akashlevy/NEM-Relay-CAD/figures/3d-cgra.pdf

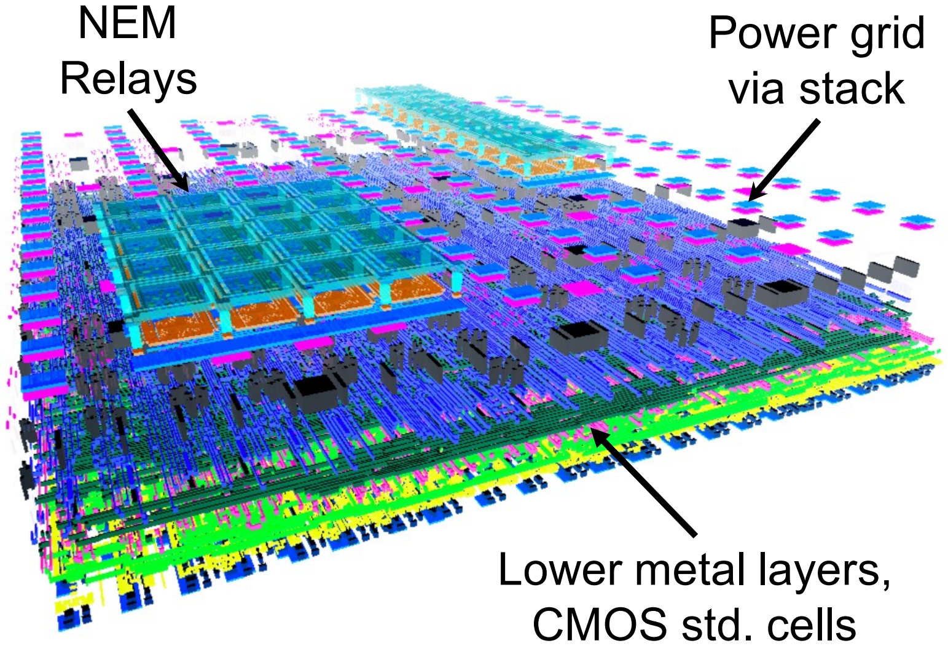
[picture p6: page 1]

NEM
Relays

Lower metal layers,
CMOS std. cells

Power grid
via stack
