akashlevy/NEM-Relay-CAD/figures/area-utilization.pdf

[7] This
work

Plate
Area
Total
Area

+40%
area util.

Area utilization: 0.33 Area utilization: 0.54
