akashlevy/NEM-Relay-CAD/figures/nem-mux-1.pdf

## Input Bits

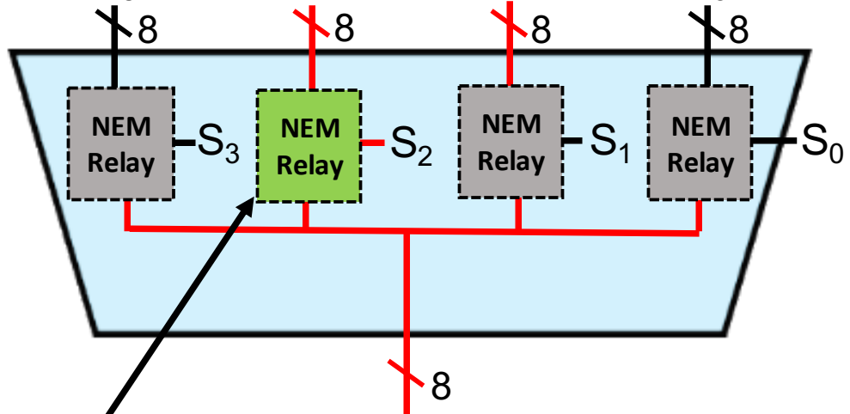
[picture p7: figure]
NEM Relay

## NEM Relay One-Hot

Output Bits | Mux (8-bit)

Example Signals:
Red=Hi, Black=Lo

Relays:
Green=ON state
Gray=OFF state

## I0 I1 I2 I3

Z

### Relay passes signal I2 through to Z pin
