akashlevy/NEM-Relay-CAD/figures/ppa-benefits.pdf

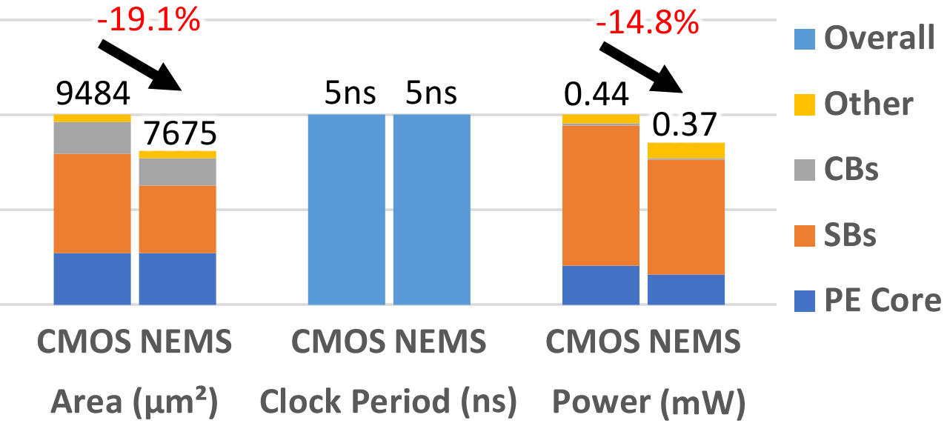
[picture p8: figure]
CMOS NEMS; Area (µm²) Clock Period; Power; Overall Other CBs SBs PE Core
