akashlevy/NEM-Relay-CAD/figures/nem-mux-2.pdf

## NEM Relay Implementation

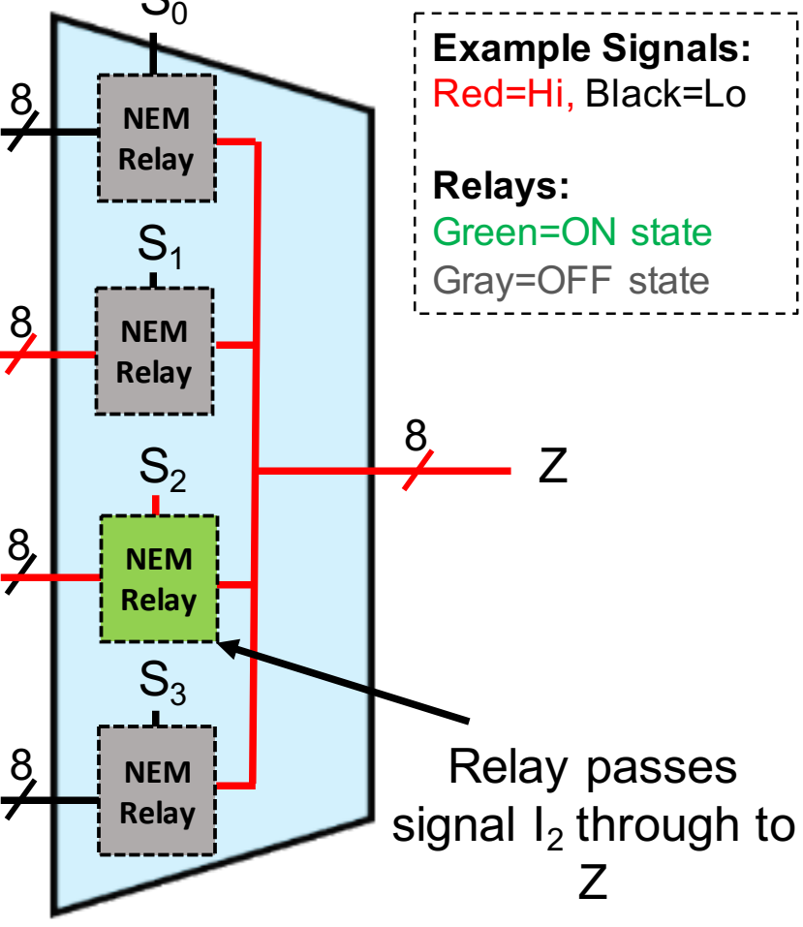
[picture p9: figure]
Example Signals: Red=Hi, Black=Lo; Relays: Green=ON state Gray=OFF state; NEM Relay; Relay passes signal I2 through to Z

I0

I1

I2

I3

S0
