akashlevy/NEM-Relay-CAD/figures/nem-mux-3.pdf

## NEM Relay Implementation

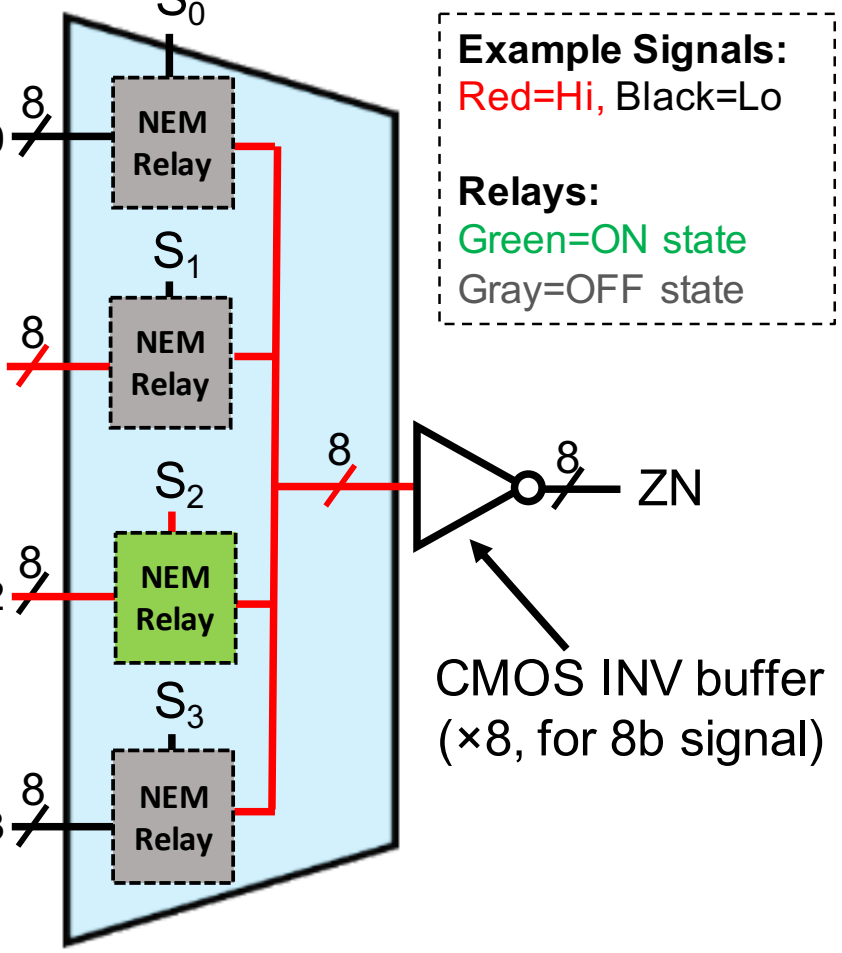
[picture p10: figure]
Example Signals: Red=Hi, Black=Lo; Relays: Green=ON state Gray=OFF state; NEM Relay; CMOS INV buffer (×8, for 8b signal)

I0

I1

I2

I3

S0
