akashlevy/NEM-Relay-CAD/figures/nem-mux-internals.pdf

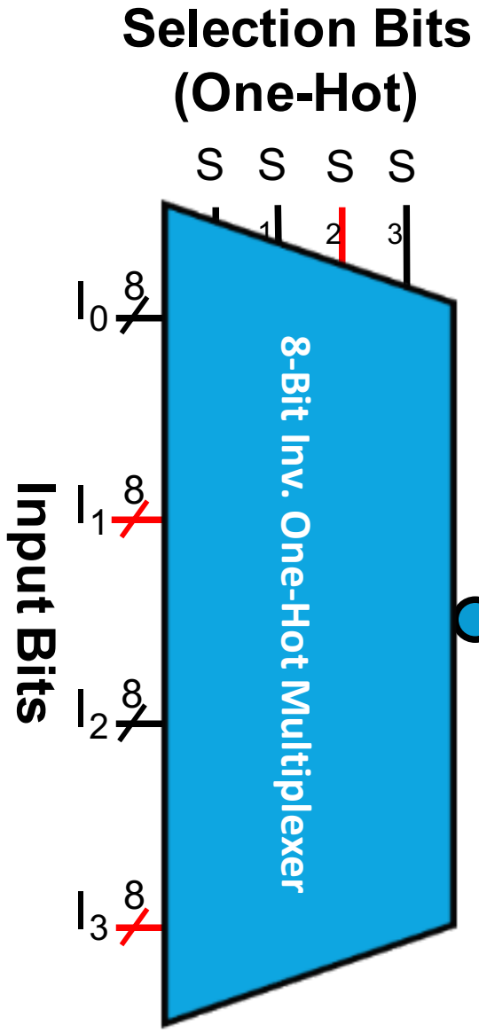
[picture p11: figure]
Selection Bits (One-Hot); Input Bits; 8 -Bit Inv. One; -Hot Multiplexer
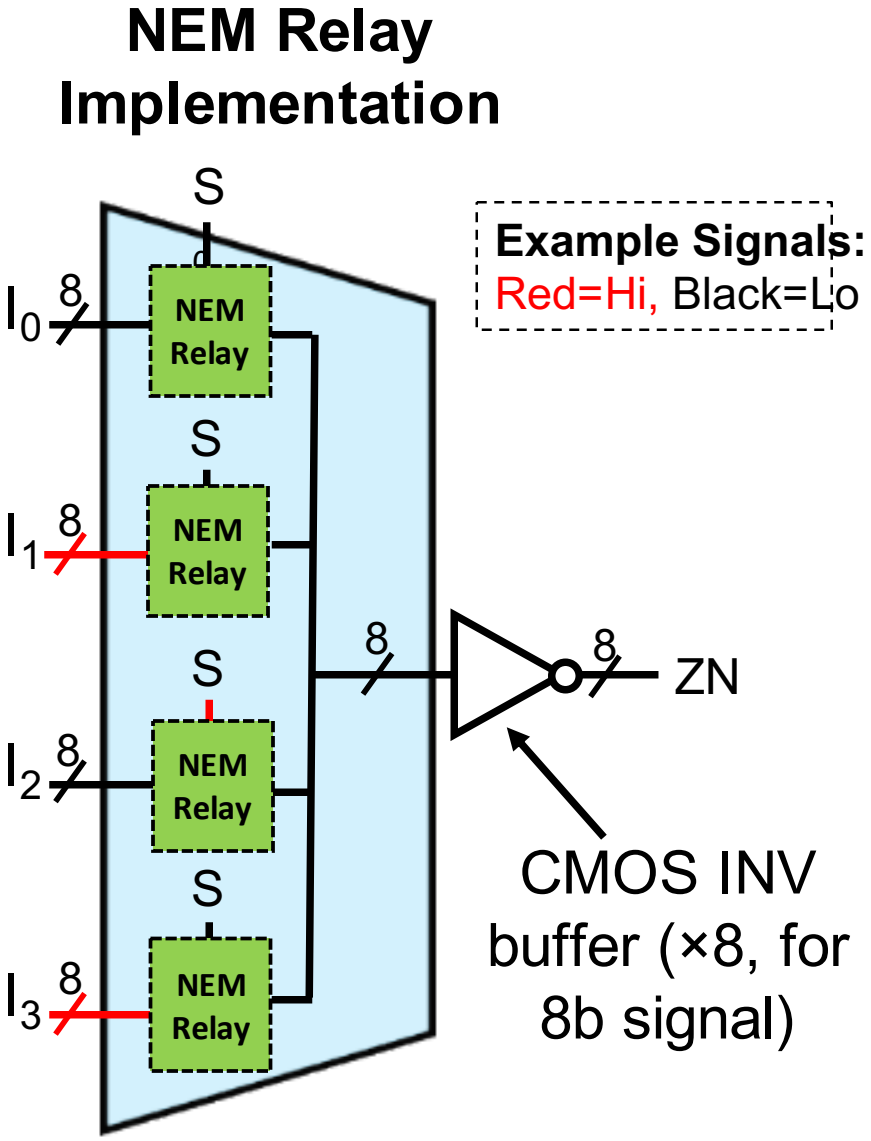
[picture p12: figure]
NEM Relay Implementation; Example Signals: Red=Hi, Black=Lo I0; NEM Relay; CMOS INV buffer (×8, for 8b signal)

8
ZN

Output Bits
