akashlevy/NEM-Relay-CAD/figures/nems-mux-3.pdf

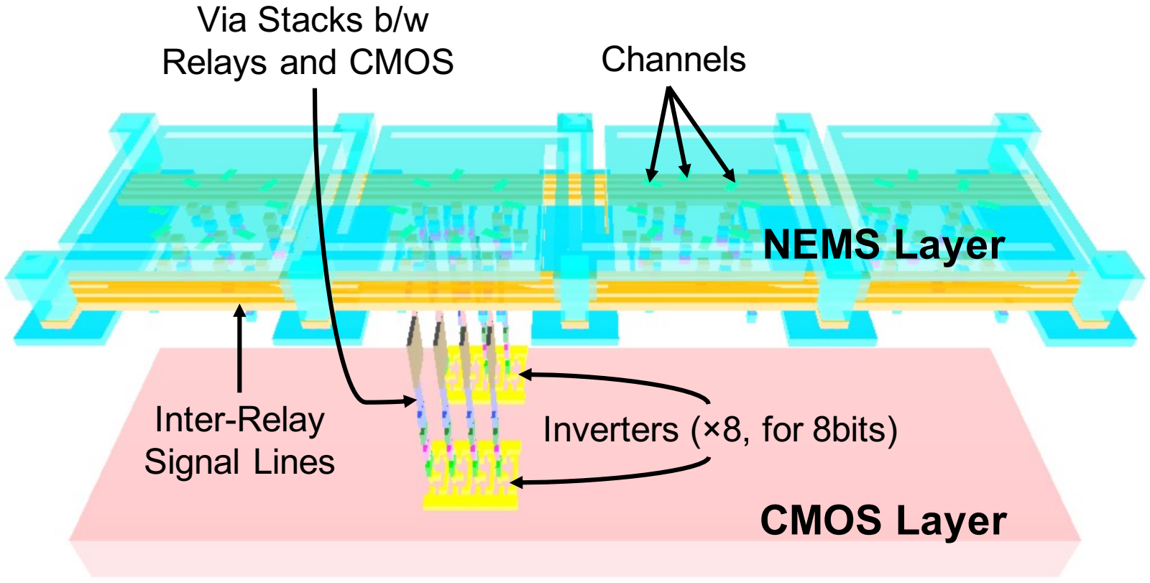
[picture p13: page 1]

CMOS Layer

NEMS Layer

Inter-Relay
Signal Lines

Via Stacks b/w
Relays and CMOS | Channels

Inverters (×8, for 8bits)
