akashlevy/NEM-Relay-CAD/figures/power-plot.pdf

0

20

40

60

80

Total Power (mW)

Cascade Conv 3×3 | Harris CMOS NEMS | CMOS NEMS | CMOS NEMS

CBs
Other
PE Core
SB

Module
