akashlevy/NEM-Relay-CAD/figures/power.pdf

0

20

40

60

80

Total Power (mW)

CMOS

NEMS

Conv 3×3

CMOS

NEMS

Cascade

CMOS

NEMS

Harris

CBs
Other
PE Core
SB

Module
