akashlevy/NEM-Relay-CAD/figures/layout-1.pdf

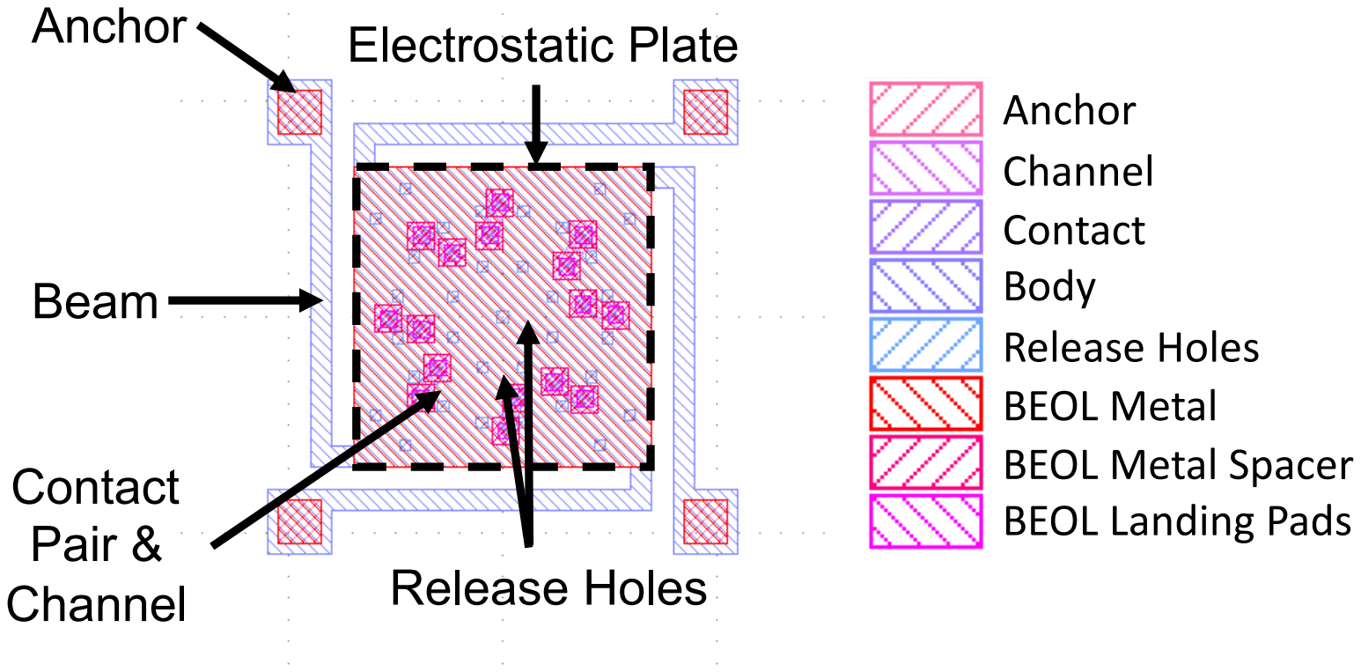
[picture p14: page 1]

Anchor
Channel
Contact
Body
Release Holes
BEOL Metal
BEOL Metal Spacer
BEOL Landing Pads

Anchor

Beam

Contact
Pair &
Channel | Release Holes

Electrostatic Plate
