akashlevy/NEM-Relay-CAD/figures/relay-layout.pdf

(a)

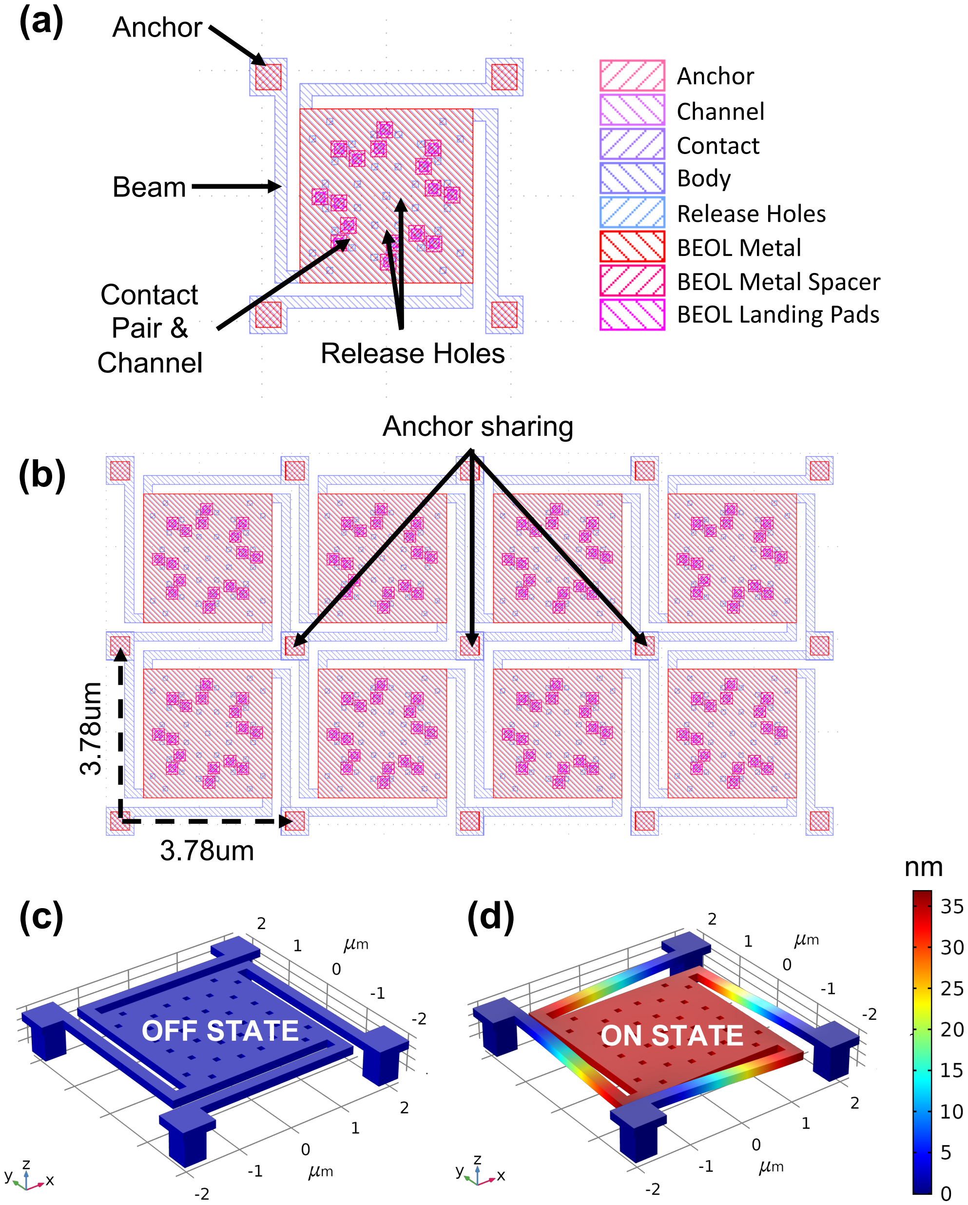
[picture p15: page 1]

Anchor
Channel
Contact
Body
Release Holes
BEOL Metal
BEOL Metal Spacer
BEOL Landing Pads

Anchor

Beam

Contact
Pair &
Channel | Release Holes

(b)

| Anchor sharing
OFF STATE | ON STATE
(c) (d)

nm

3.78u

m

3.78um
