akashlevy/NEM-Relay-CAD/figures/relay-side-view-mp-cartoon.pdf

S1 | G | D1

B

Channel

Dielectric Spacer

S2 | G | D2

Channel

G
