akashlevy/NEM-Relay-CAD/figures/transient-curve-rise.pdf

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

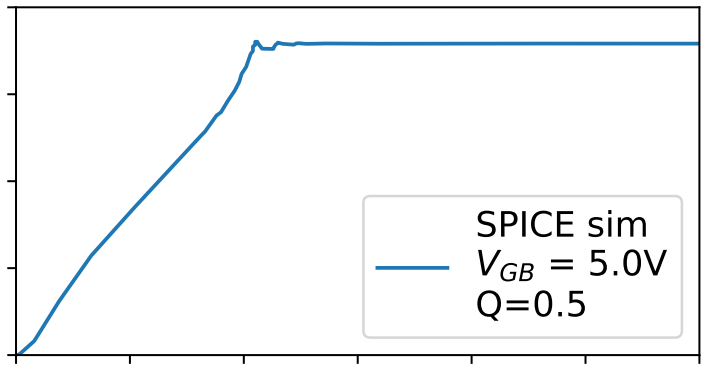
[picture p18: figure]
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
