akashlevy/NEM-Relay-CAD/figures/contact-variation.pdf

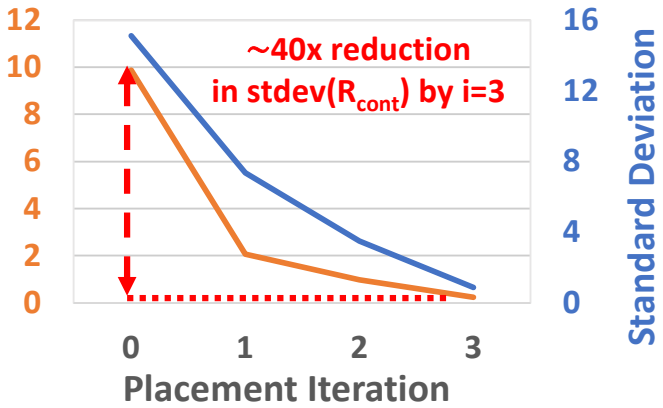
[picture p19: figure]
Standard Deviation; Placement Iteration ∼40x reduction in stdev(Rcont) by i=3

### of Fcont (nN)

Standard Deviation

### of Rcont (Ω)
