akashlevy/NEM-Relay-CAD/figures/layout-2.pdf

…

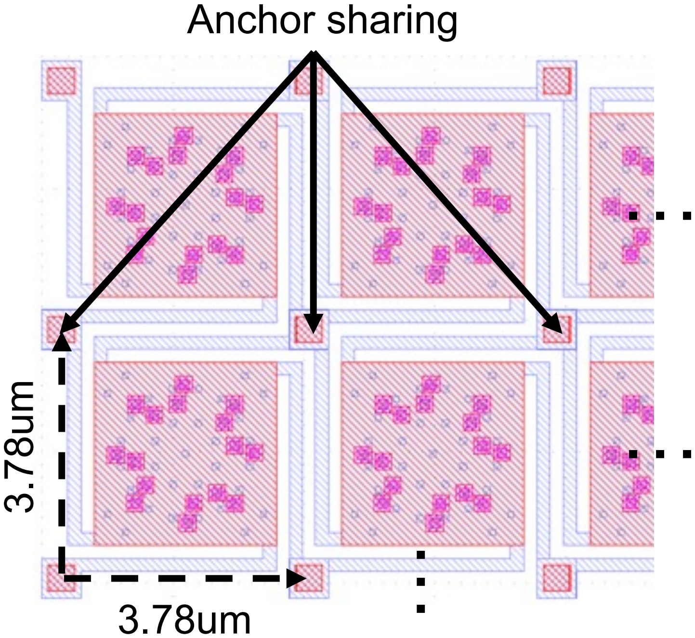
[picture p20: page 1]

Anchor sharing

3.78um

3.78um

…

…
