akashlevy/NEM-Relay-CAD/figures/area-2.pdf

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

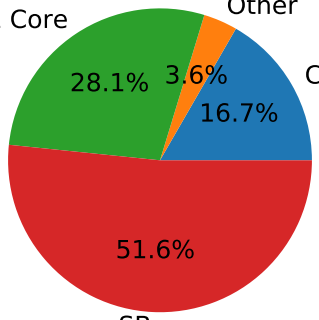
[picture p21: figure]
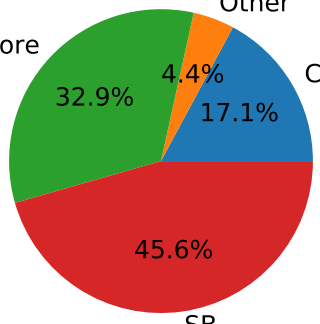
[picture p22: figure]
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
