akashlevy/NEM-Relay-CAD/figures/area-breakdown.pdf

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

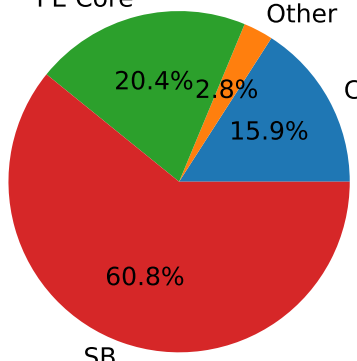
[picture p23: figure]
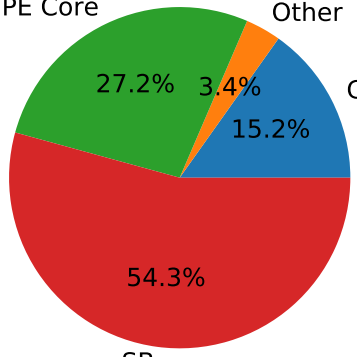
[picture p24: figure]
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
