akashlevy/NEM-Relay-CAD/figures/delay-2.pdf

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

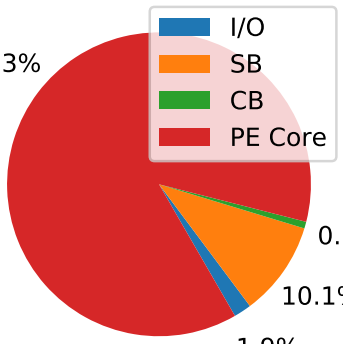
[picture p25: figure]
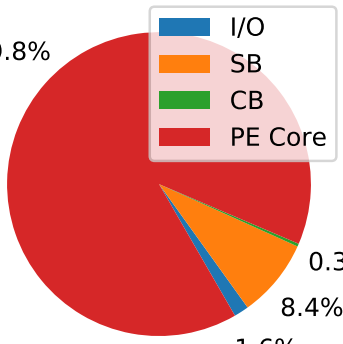
[picture p26: figure]
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
