akashlevy/NEM-Relay-CAD/figures/power-breakdown.pdf

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

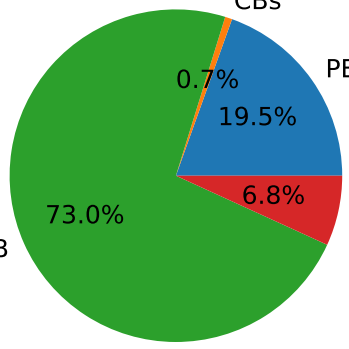
[picture p27: figure]
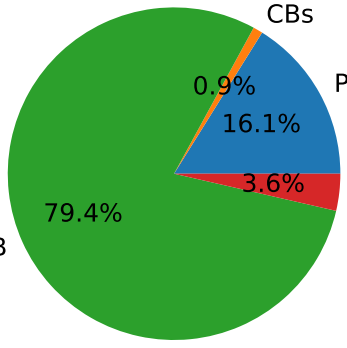
[picture p28: figure]
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
