akashlevy/NEM-Relay-CAD/figures/layout-3.pdf

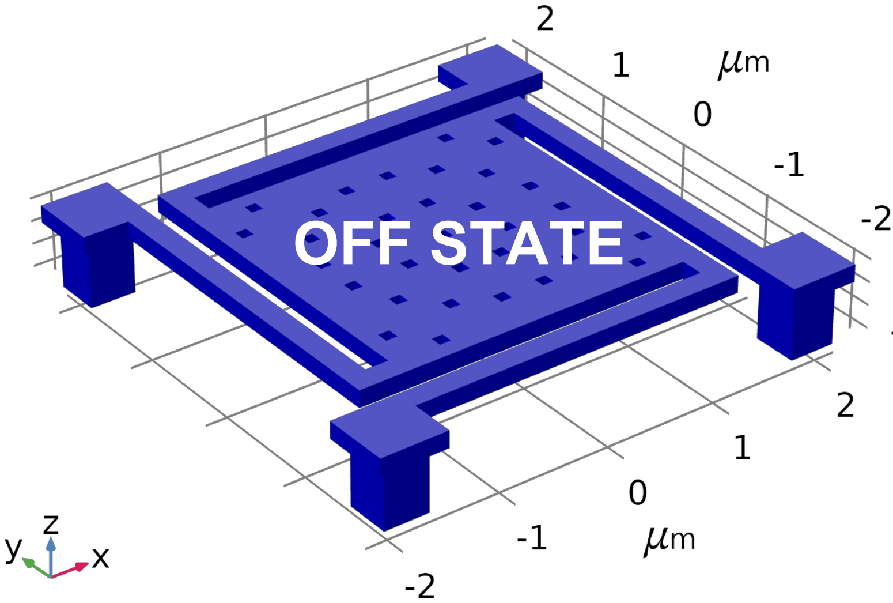
[picture p29: page 1]

OFF STATE
