akashlevy/NEM-Relay-CAD/figures/layout-4.pdf

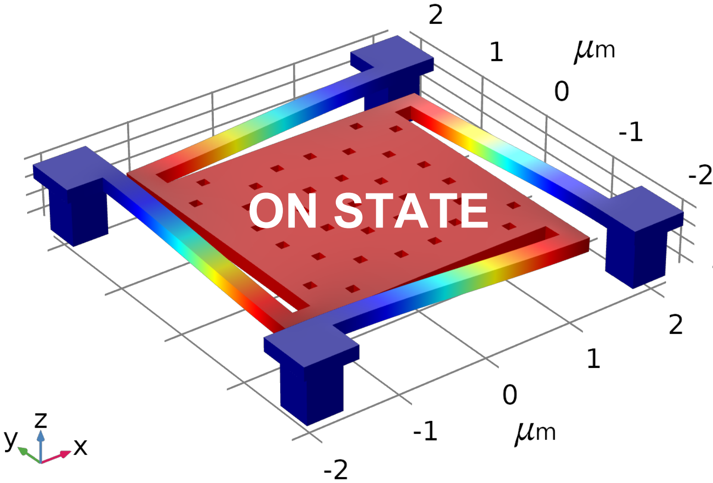
[picture p30: page 1]

ON STATE
