akashlevy/NEM-Relay-CAD/figures/layout-5.pdf

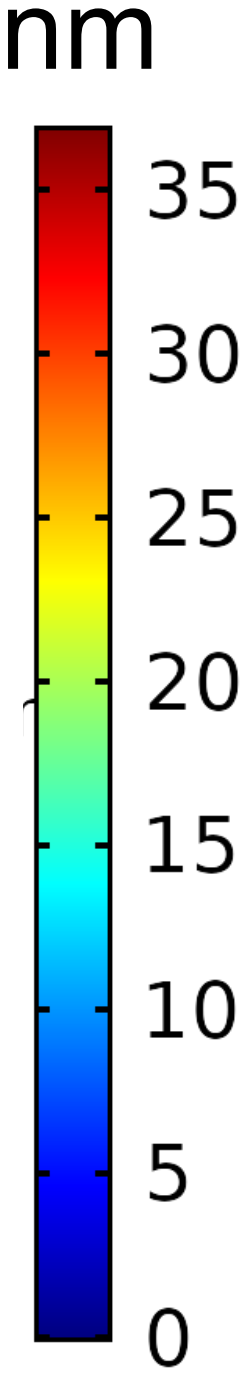
[picture p31: page 1]

nm
