akashlevy/NEM-Relay-CAD/figures/iterative-contact-placement.pdf

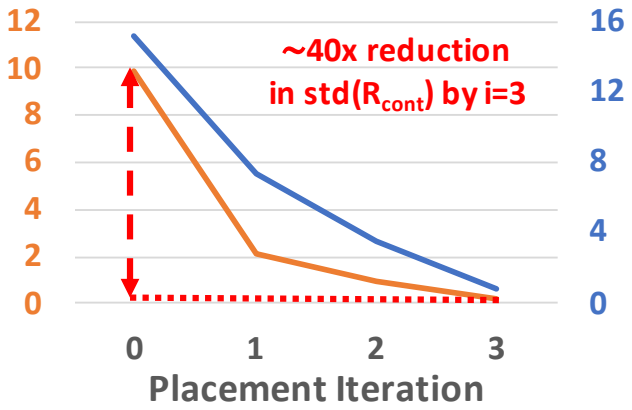
[picture p32: figure]
Placement Iteration ∼40x reduction in std(Rcont) by i=3

### Std. of Fcont (nN)

### Std. of Rcont (Ω)
