akashlevy/NEM-Relay-CAD/figures/3d-cgra.png

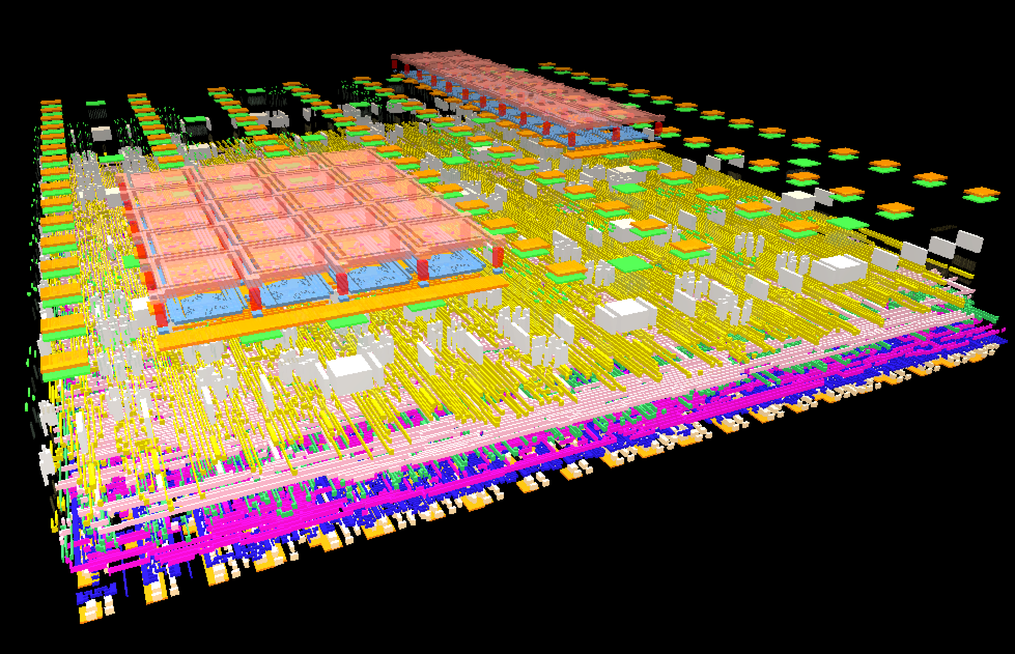
figures/3d-cgra.png
