akashlevy/NEM-Relay-CAD/figures/cccp-hor.png

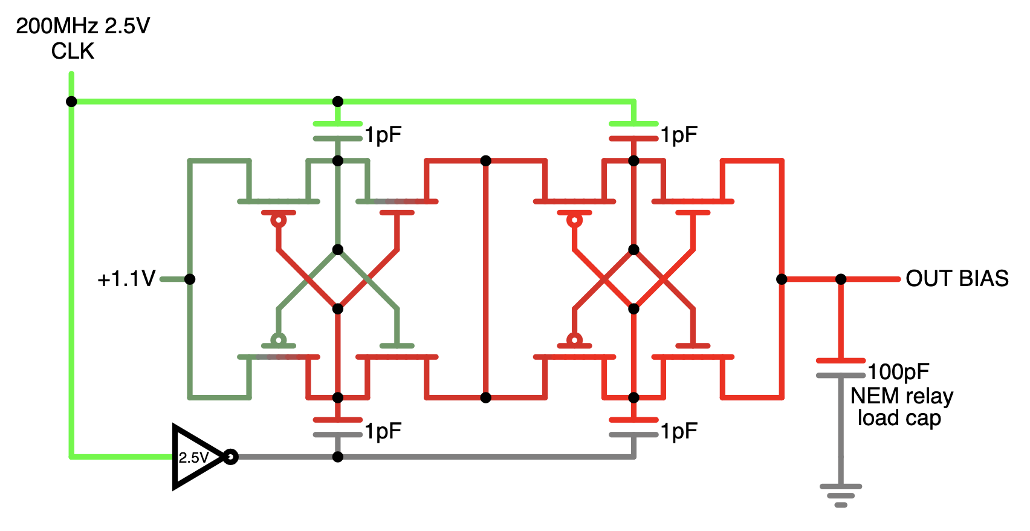
figures/cccp-hor.png
