akashlevy/NEM-Relay-CAD/figures/cccp-vert.png

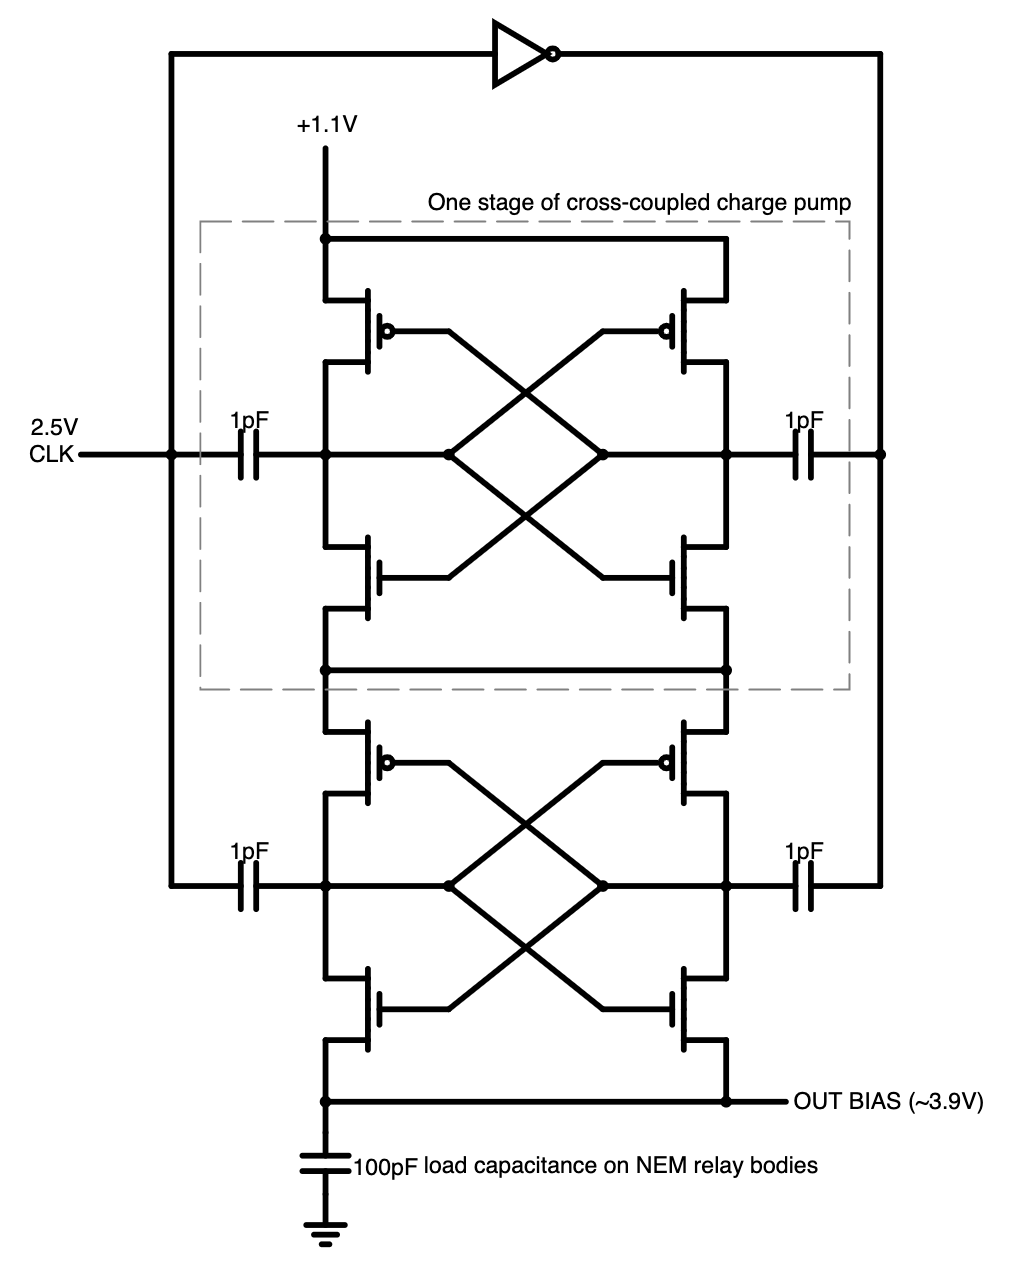
figures/cccp-vert.png
