akashlevy/NEM-Relay-CAD/figures/cpump-diode-circuit.png

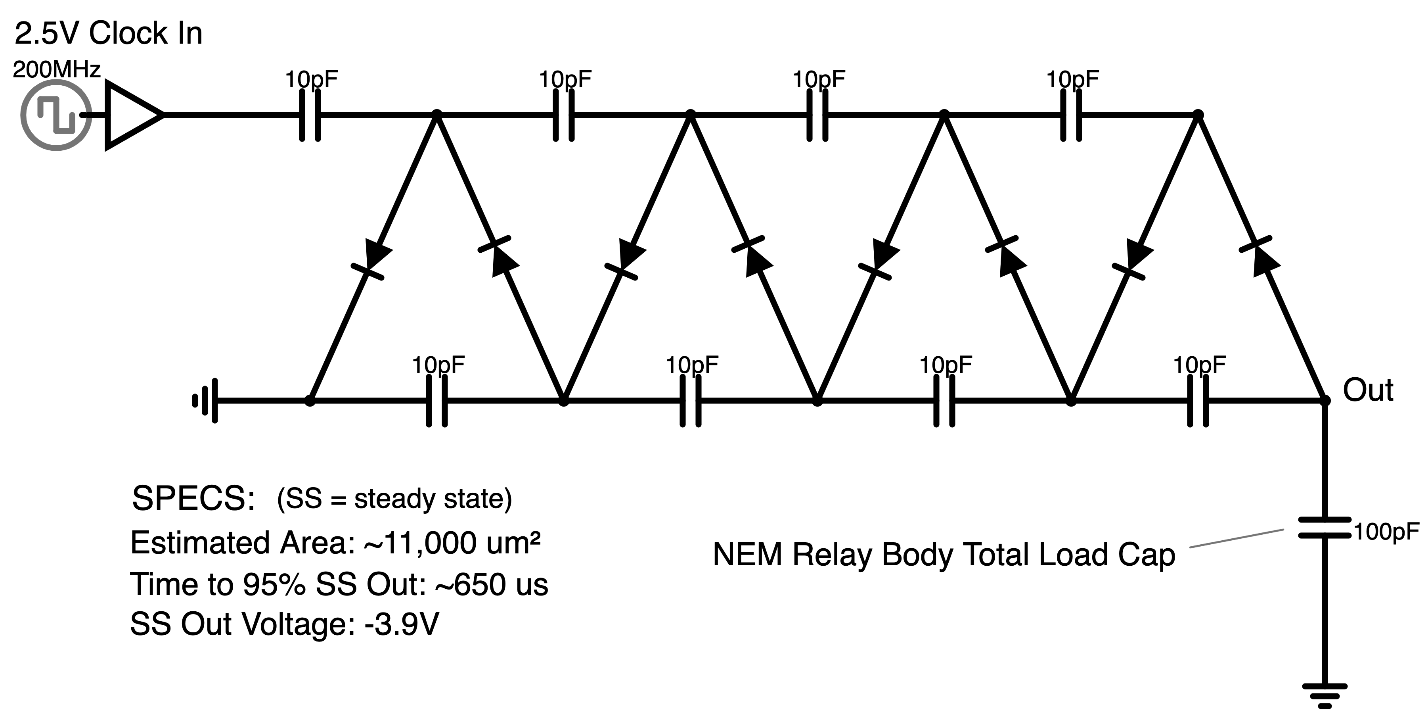
figures/cpump-diode-circuit.png
