akashlevy/NEM-Relay-CAD/figures/displacement-contour.png

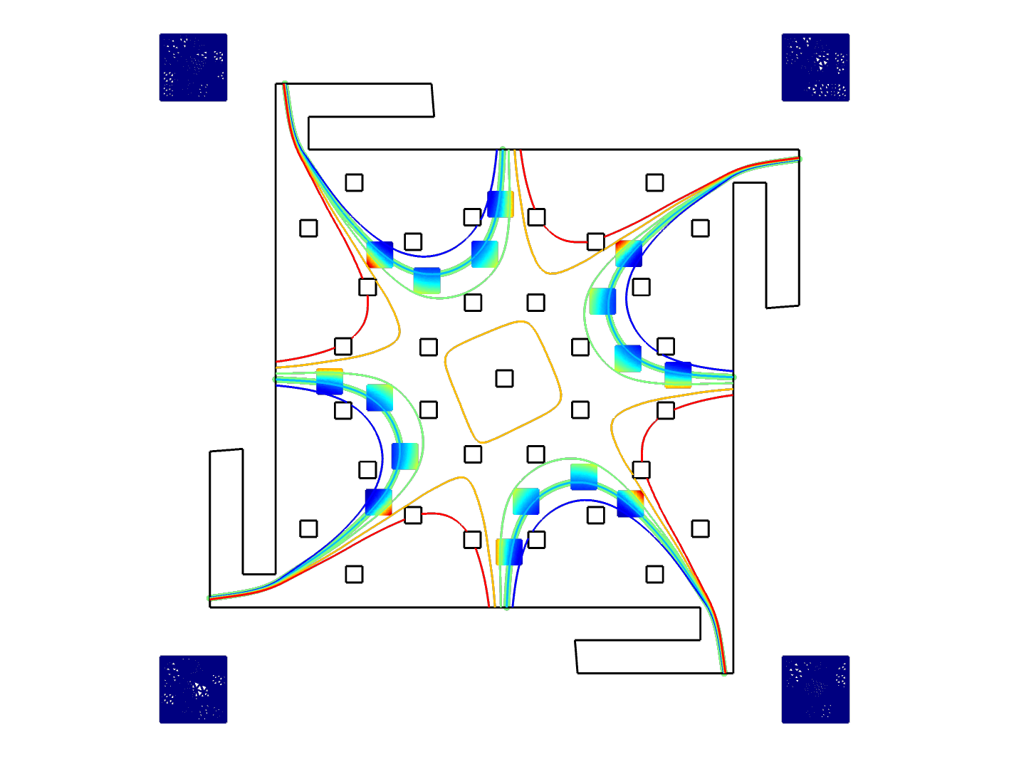
figures/displacement-contour.png
