akashlevy/NEM-Relay-CAD/figures/fluid/combined.png

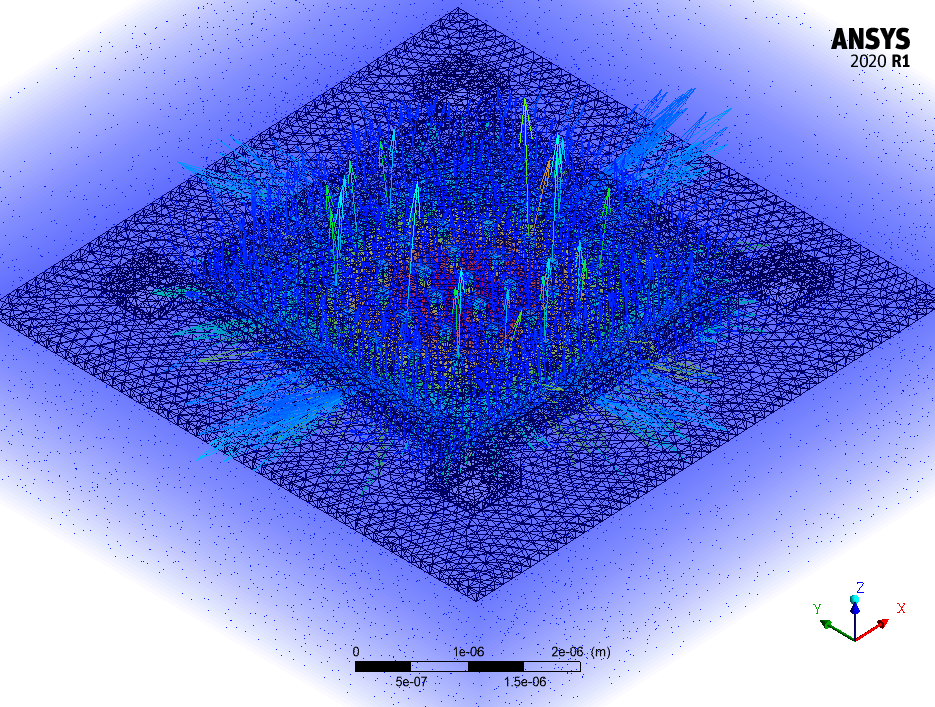
figures/fluid/combined.png
