akashlevy/NEM-Relay-CAD/figures/fluid/pressure-contour.png

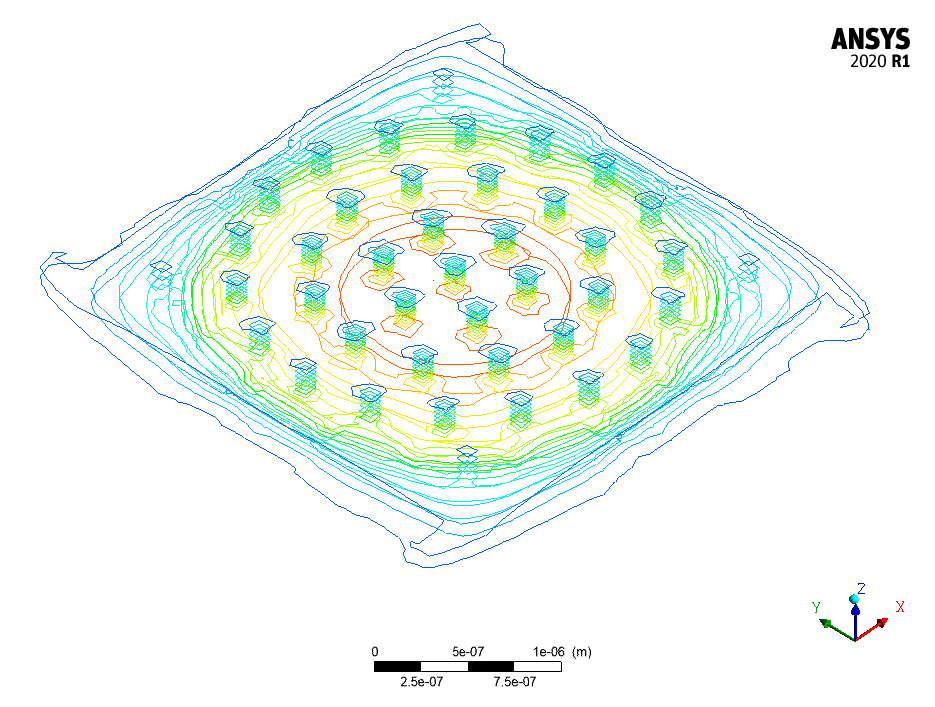
figures/fluid/pressure-contour.png
