akashlevy/NEM-Relay-CAD/figures/fluid/pressure.png

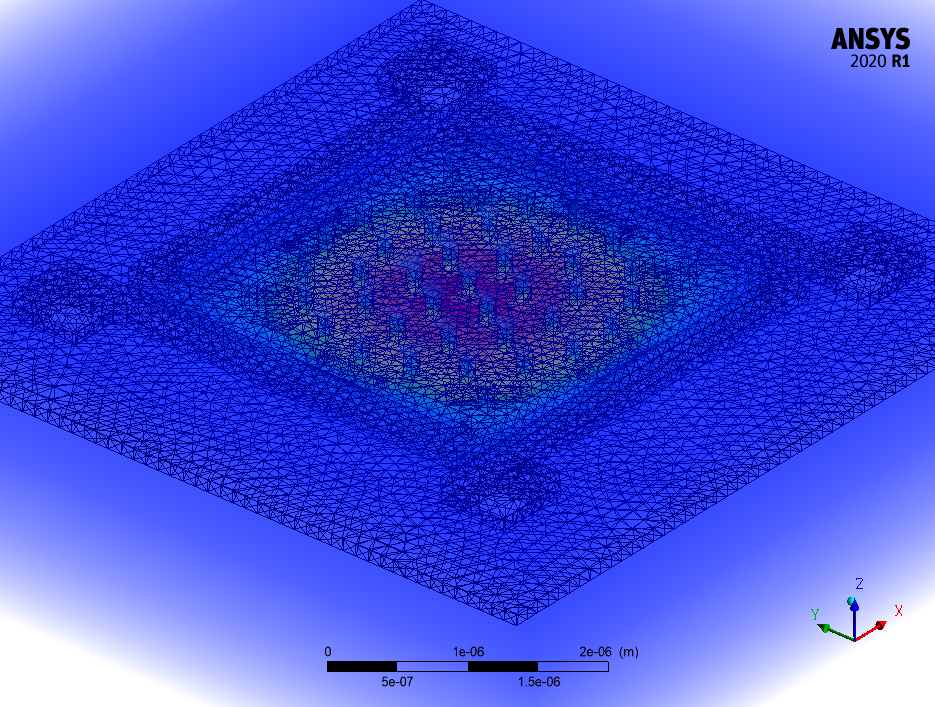
figures/fluid/pressure.png
