akashlevy/NEM-Relay-CAD/figures/fluid/velocity.png

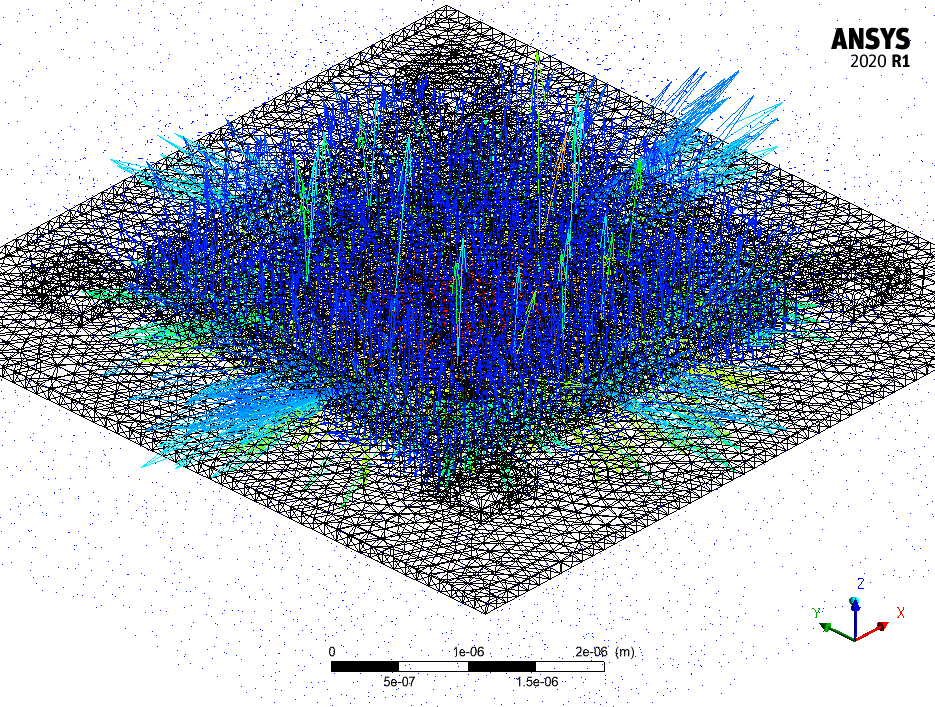
figures/fluid/velocity.png
