akashlevy/NEM-Relay-CAD/figures/GDS3D-1-dark.png

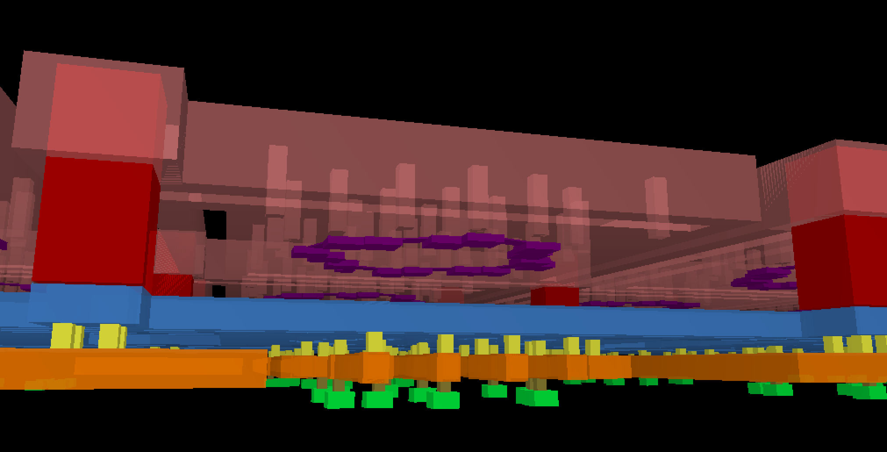
figures/GDS3D-1-dark.png
