akashlevy/NEM-Relay-CAD/figures/GDS3D-1-light.png

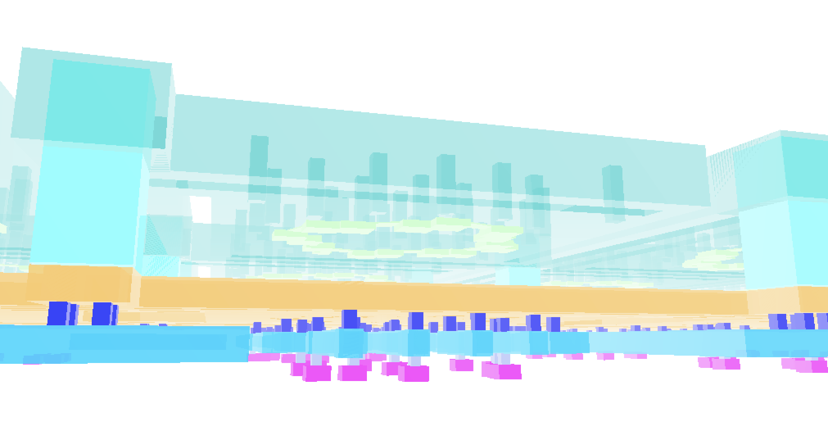
figures/GDS3D-1-light.png
