akashlevy/NEM-Relay-CAD/figures/GDS3D-2-light.png

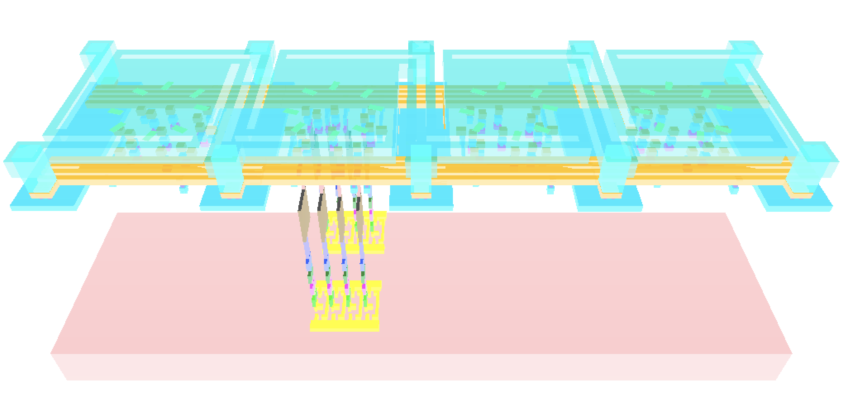
figures/GDS3D-2-light.png
