akashlevy/NEM-Relay-CAD/figures/GDS3D-2.png

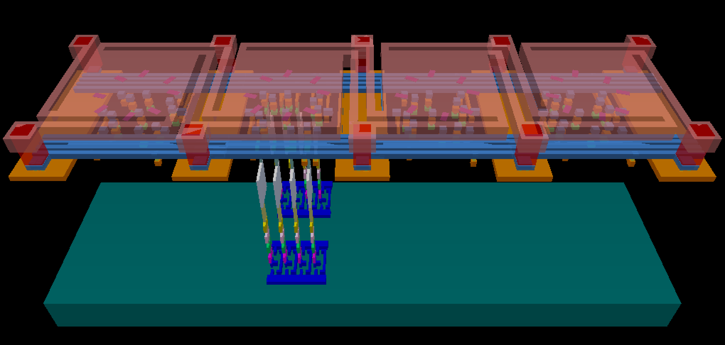
figures/GDS3D-2.png
