akashlevy/NEM-Relay-CAD/figures/gds3d-full-light.png

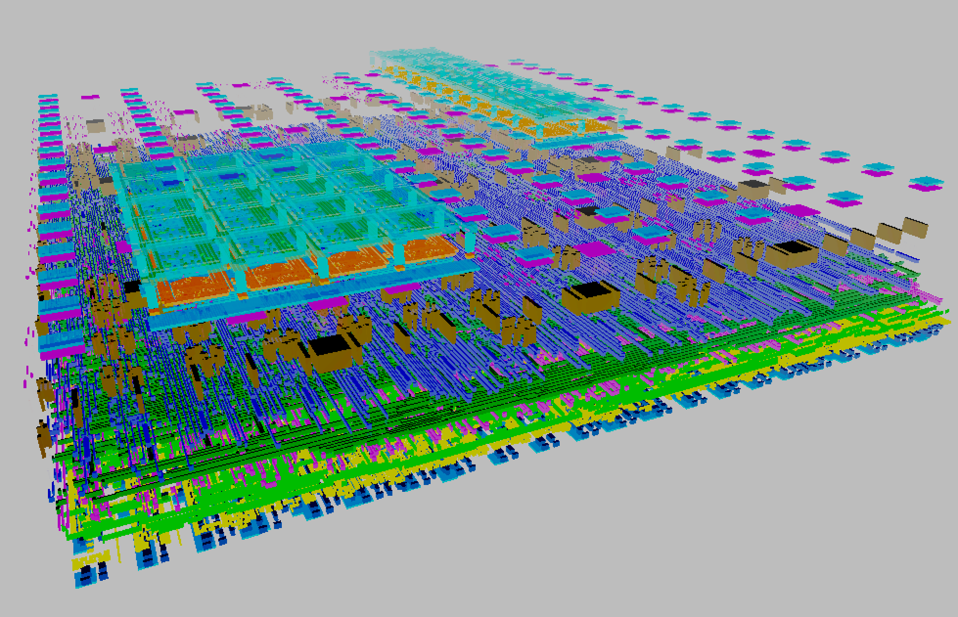
figures/gds3d-full-light.png
