akashlevy/NEM-Relay-CAD/figures/layout.png

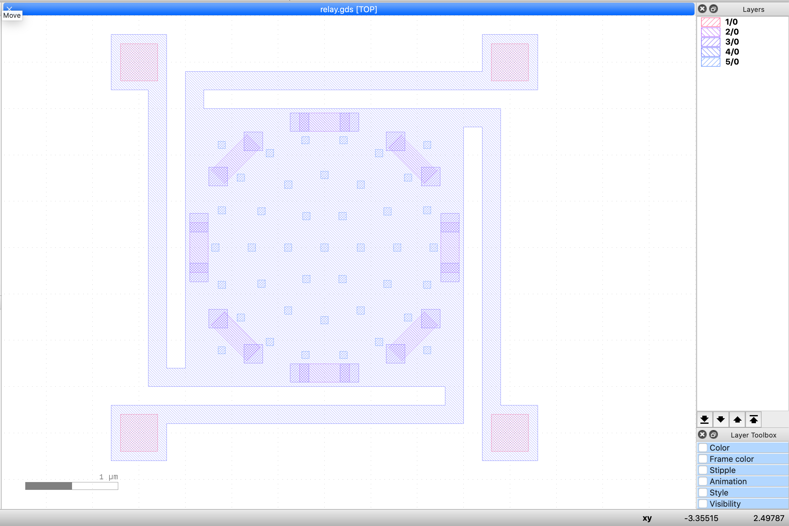
figures/layout.png
