akashlevy/NEM-Relay-CAD/figures/mesh.png

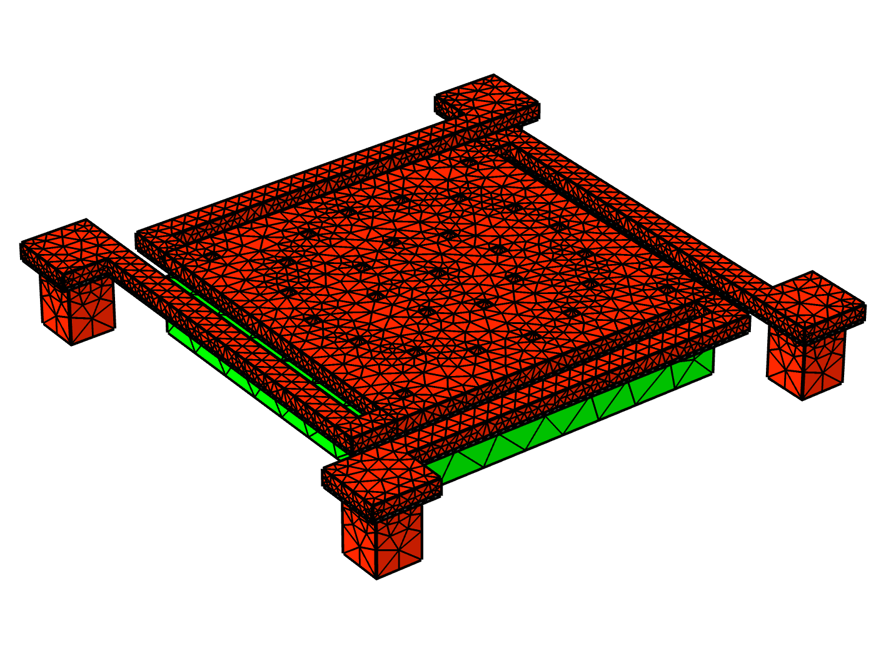
figures/mesh.png
