akashlevy/NEM-Relay-CAD/figures/mode2comsol.gif

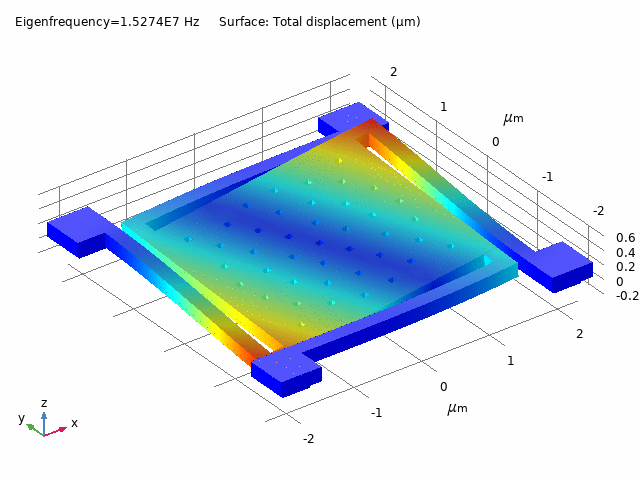
figures/mode2comsol.gif
