akashlevy/NEM-Relay-CAD/figures/mode4comsol.gif

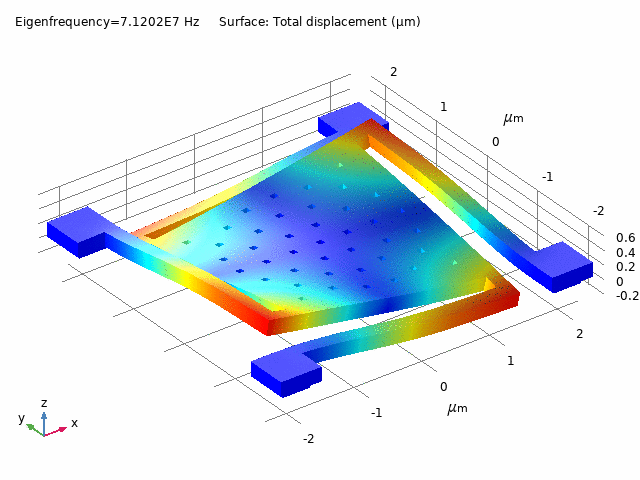
figures/mode4comsol.gif
