akashlevy/NEM-Relay-CAD/figures/mode6comsol.gif

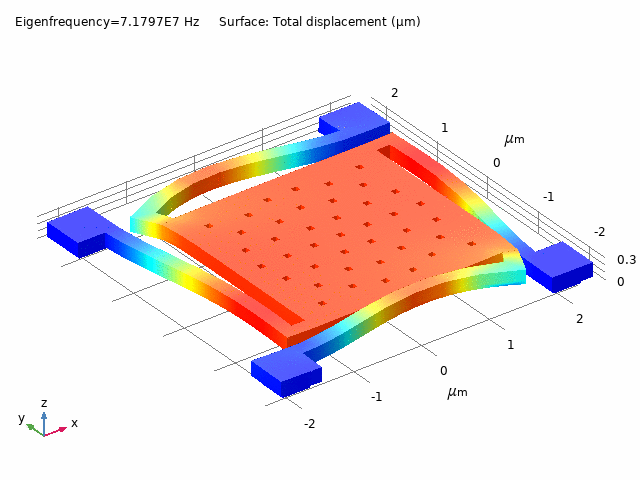
figures/mode6comsol.gif
