akashlevy/NEM-Relay-CAD/figures/mosaic.png

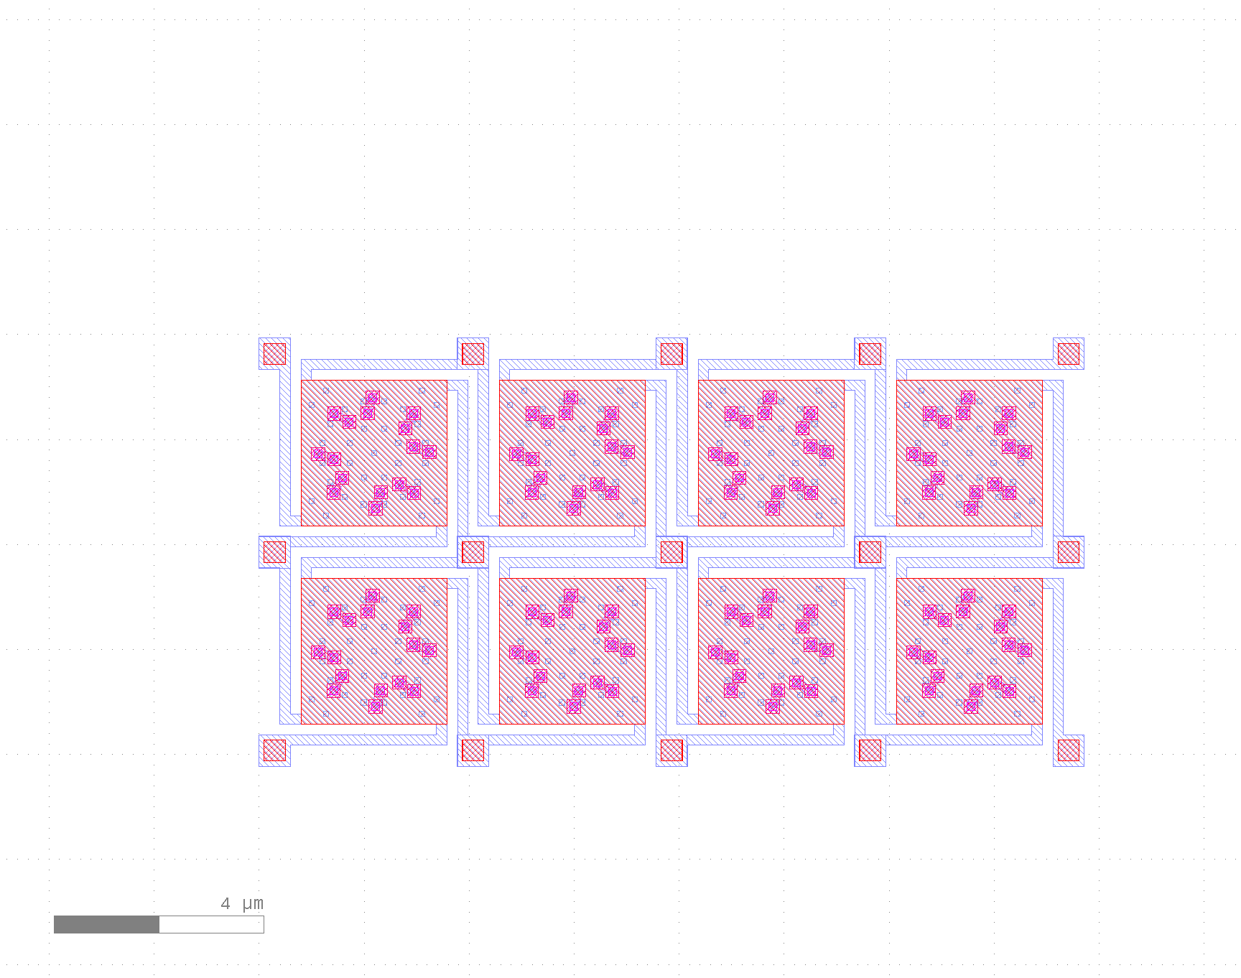
figures/mosaic.png
