akashlevy/NEM-Relay-CAD/figures/pex.gif

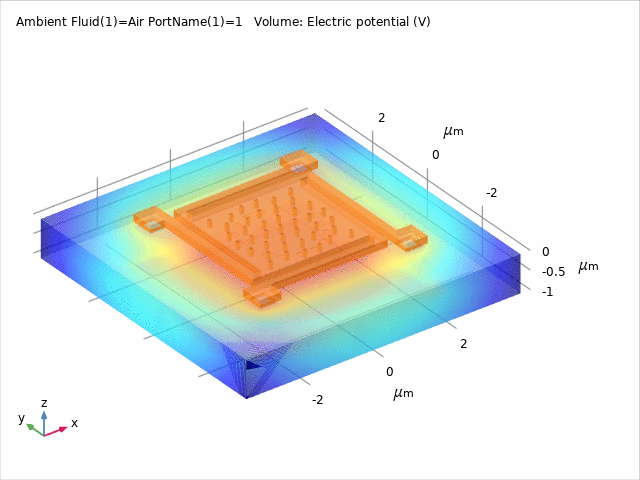
figures/pex.gif
