akashlevy/NEM-Relay-CAD/figures/quasi-static-potential.gif

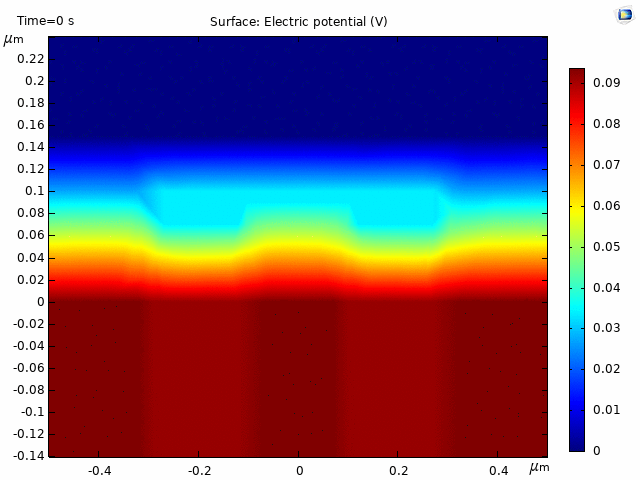
figures/quasi-static-potential.gif
