akashlevy/NEM-Relay-CAD/figures/quasistatic-curve-labeled.png

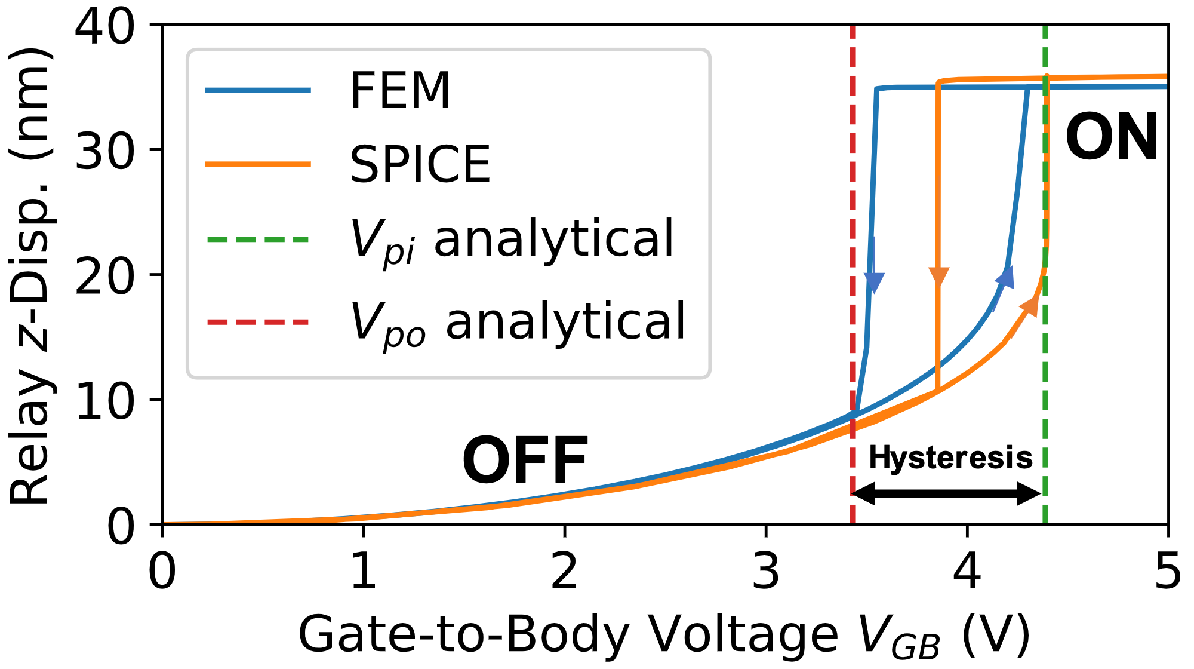
figures/quasistatic-curve-labeled.png
