akashlevy/NEM-Relay-CAD/figures/relay-perspective-cont.png

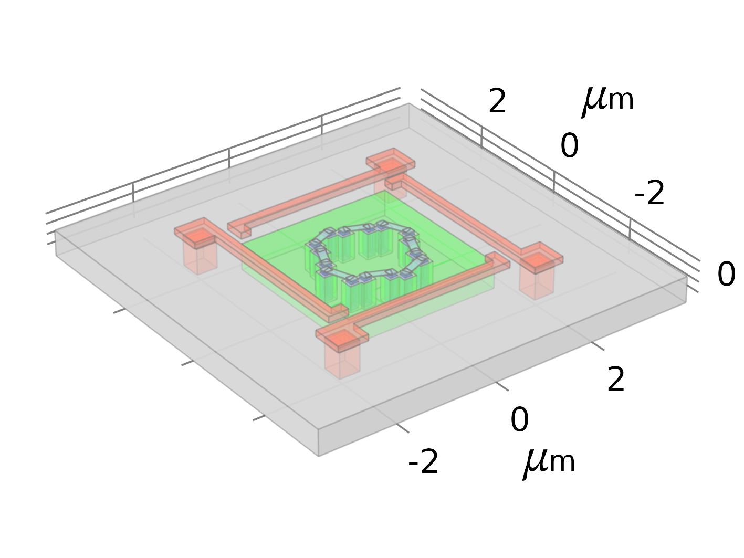
figures/relay-perspective-cont.png
