akashlevy/NEM-Relay-CAD/figures/relay-perspective.png

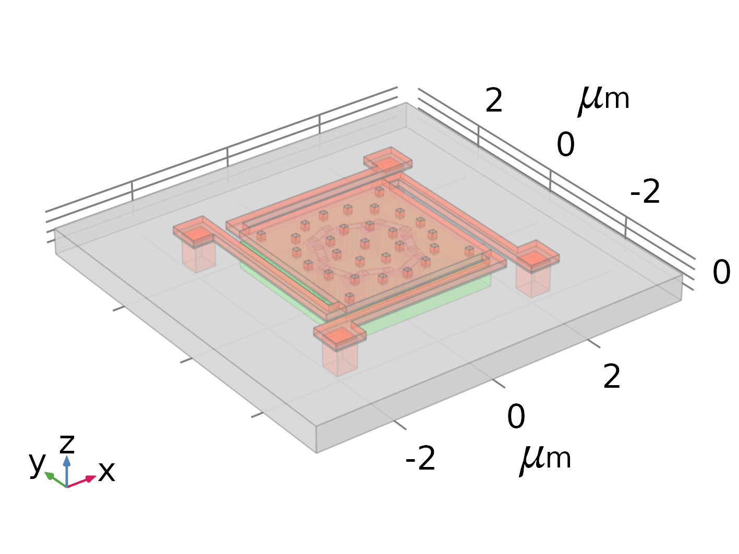
figures/relay-perspective.png
