akashlevy/NEM-Relay-CAD/figures/relay.png

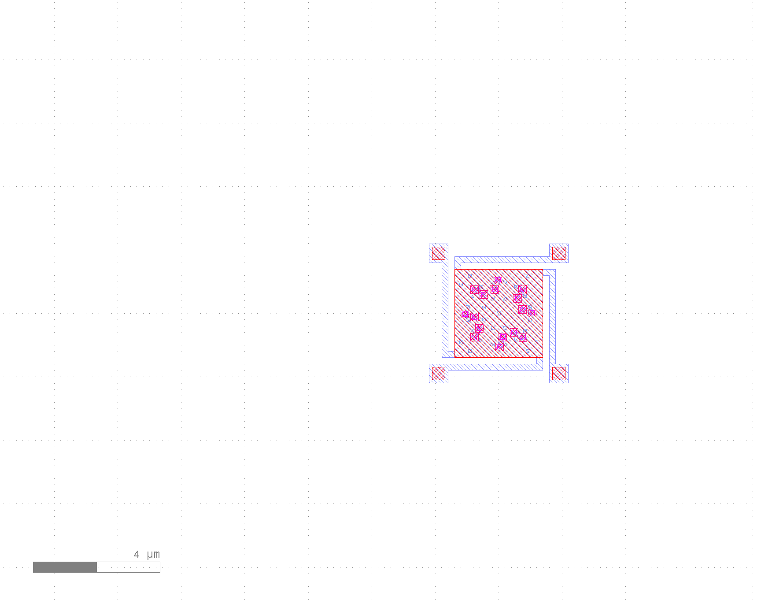
figures/relay.png
