akashlevy/NEM-Relay-CAD/output/iter0/displacement-contour-noanc.png

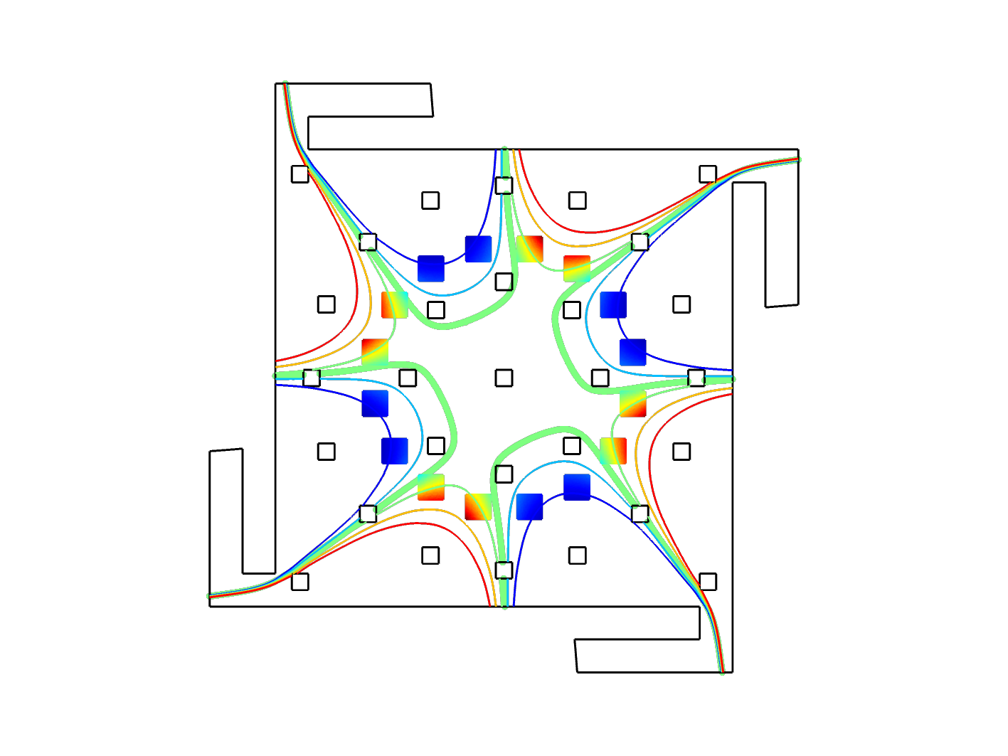
output/iter0/displacement-contour-noanc.png
