akashlevy/NEM-Relay-CAD/output/iter0/displacement-contour.png

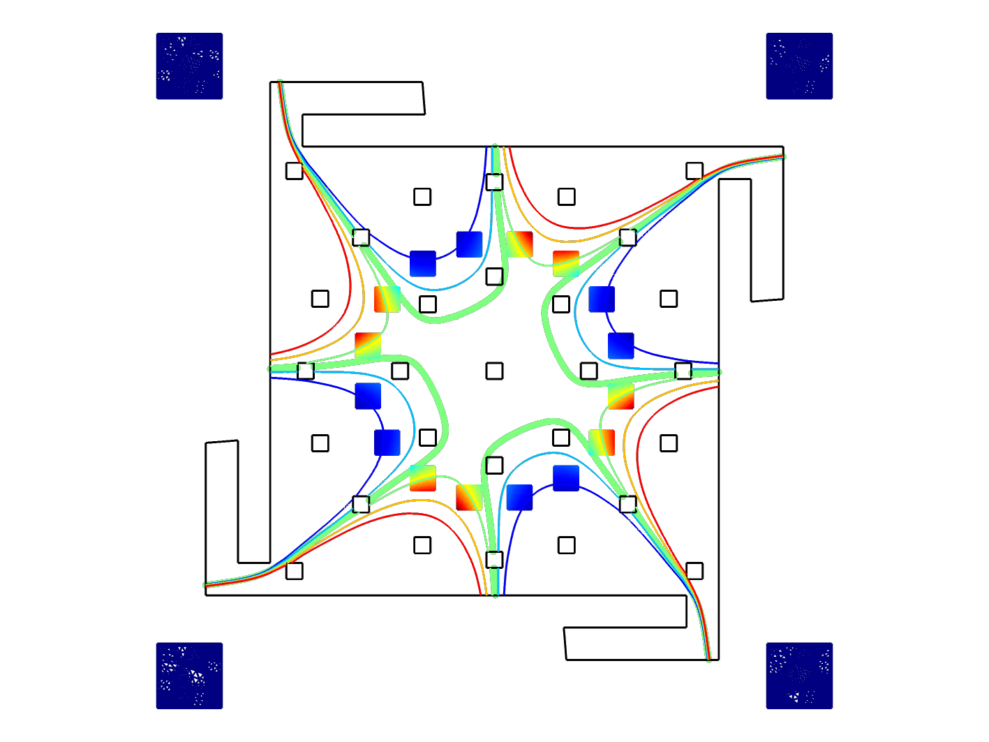
output/iter0/displacement-contour.png
