akashlevy/NEM-Relay-CAD/output/iter1/displacement-contour-noanc.png

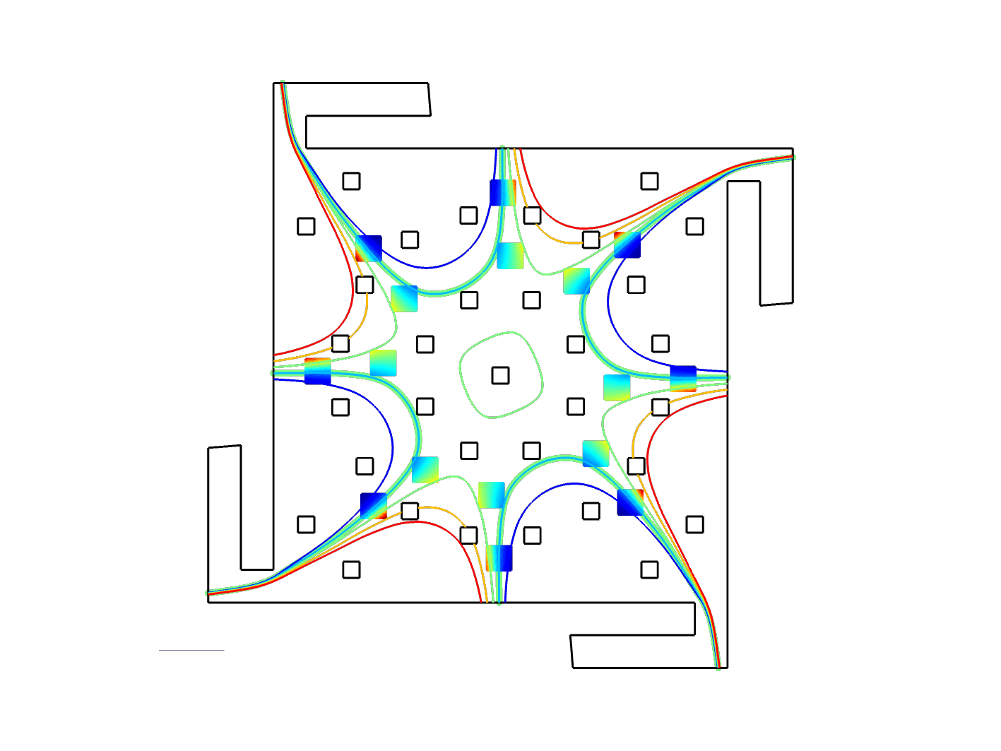
output/iter1/displacement-contour-noanc.png
