akashlevy/NEM-Relay-CAD/output/iter1/displacement-contour.png

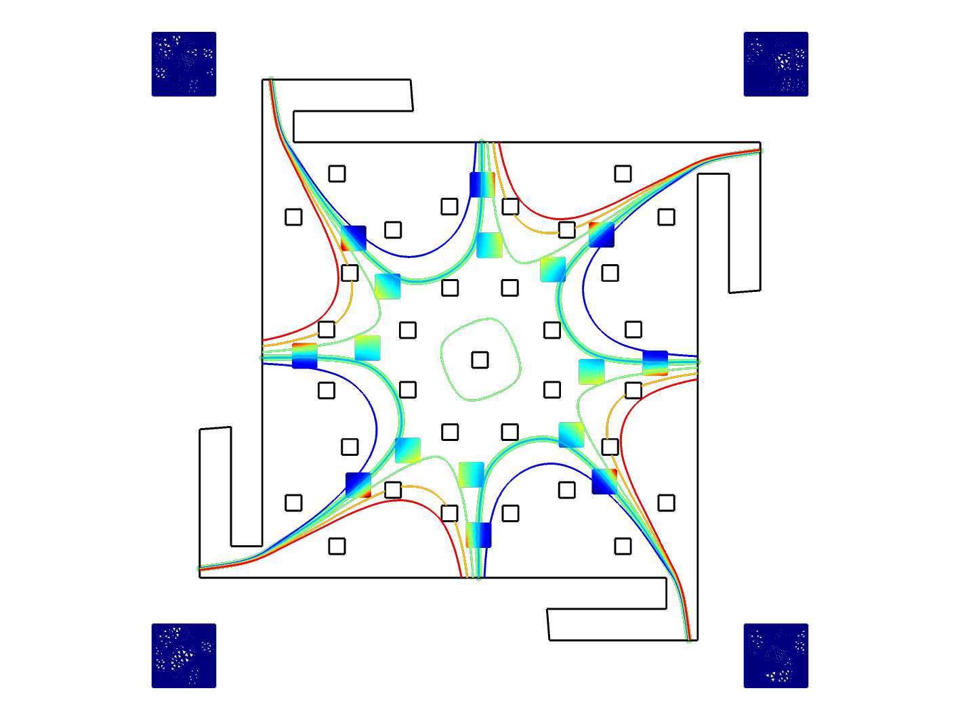
output/iter1/displacement-contour.png
