akashlevy/NEM-Relay-CAD/output/iter4/displacement-contour-noanc.png

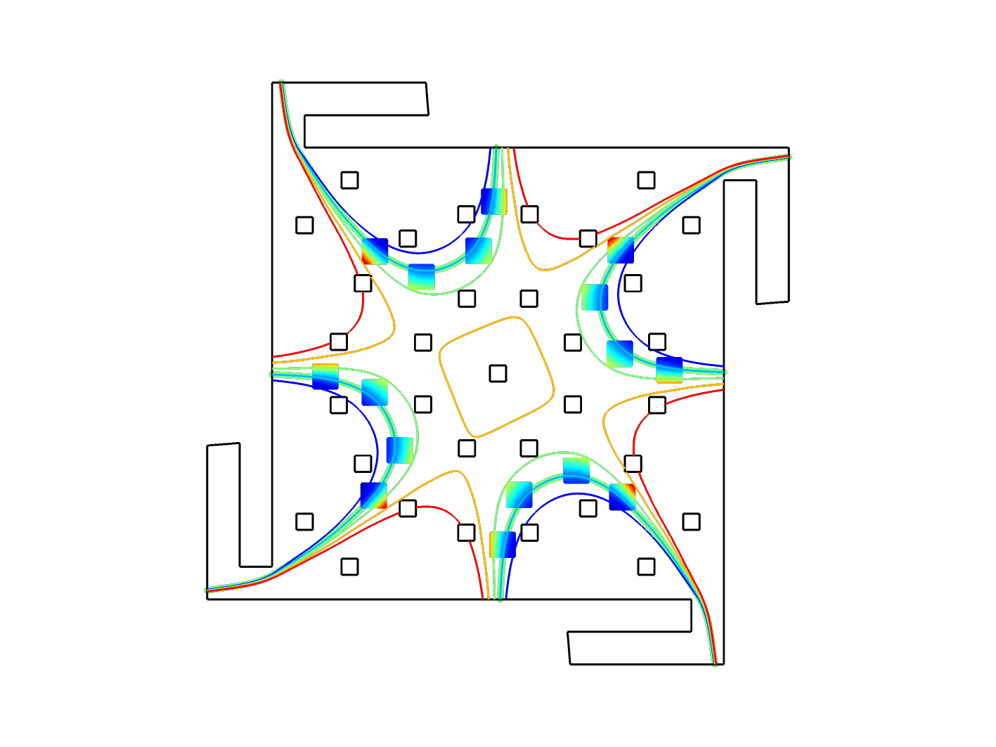
output/iter4/displacement-contour-noanc.png
