akashlevy/NEM-Relay-CAD/figures/materials.png

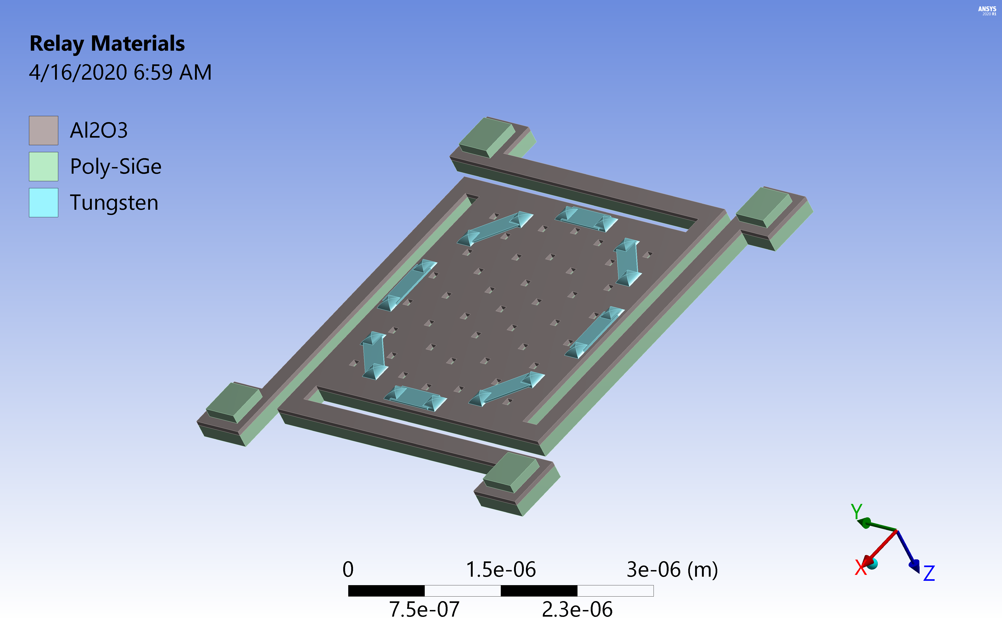
figures/materials.png
