akashlevy/NEM-Relay-CAD/figures/spice-model.pdf

### Mechanical Model

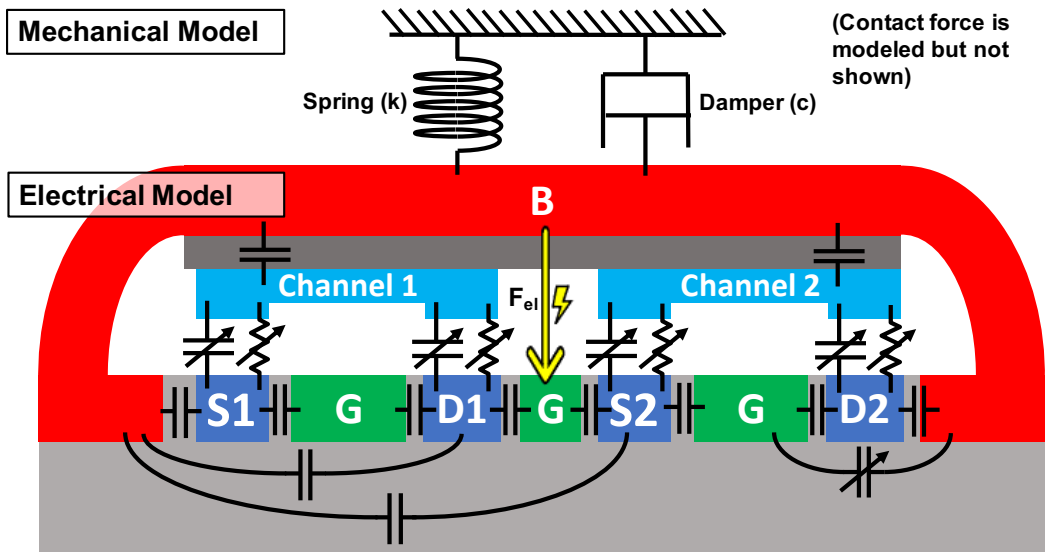
[picture p81: page 1]
Channel 1; Channel 2; Spring (k); Damper (c); Electrical Model; Fel

(Contact force is
modeled but not
shown)
