akashlevy/NEM-Relay-CAD/figures/cgra.pdf

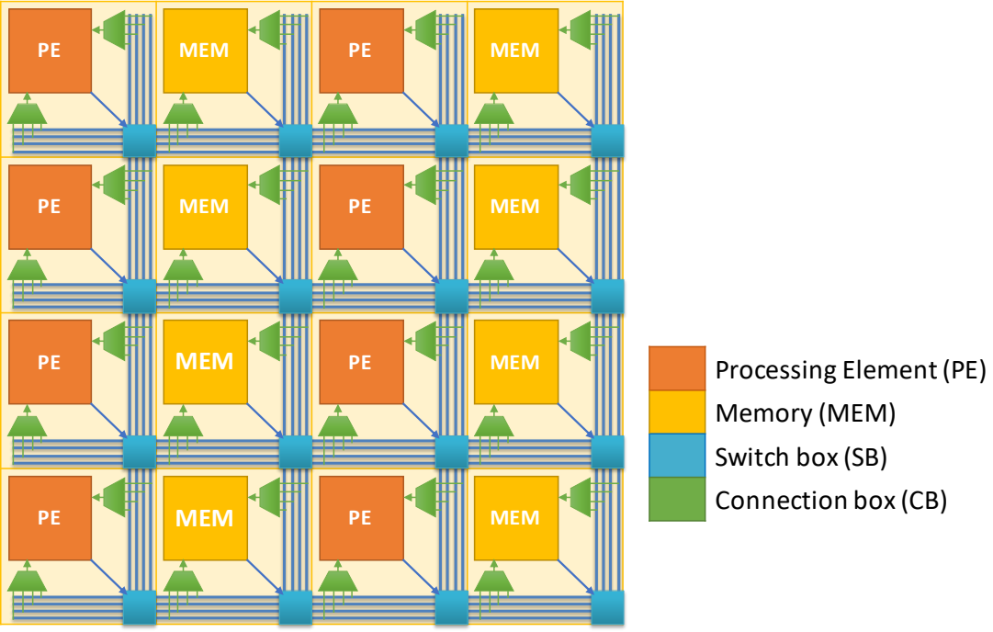
[picture p82: page 1]
MEM

Processing Element (PE)
Memory (MEM)
Switch box (SB)
Connection box (CB)
