akashlevy/NEM-Relay-CAD/figures/relay-side-view-cartoon.pdf

## OFF state

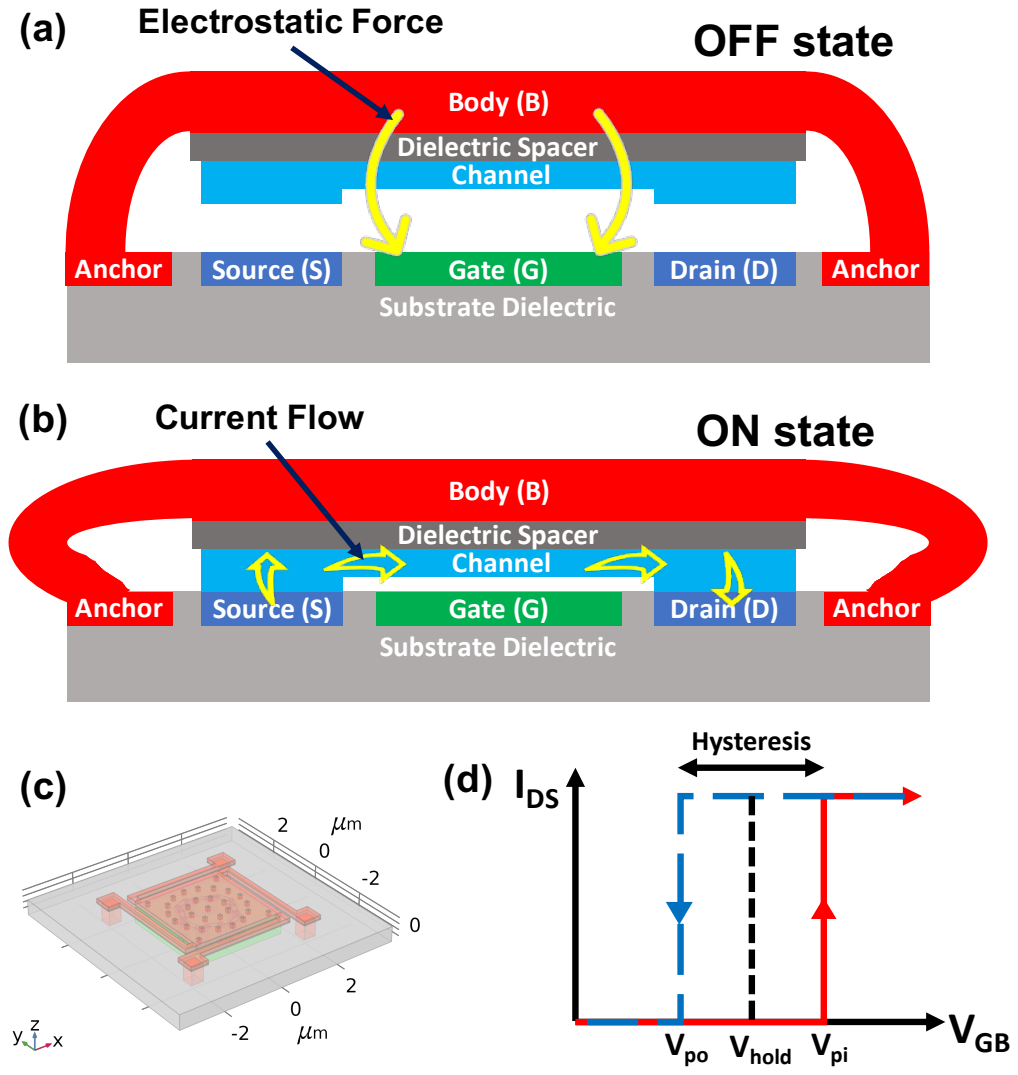
[picture p83: page 1]
Substrate Dielectric; Source (S); Gate (G); Drain (D); Body (B); Channel; Dielectric Spacer; Anchor; Current Flow; Electrostatic Force; Vpo; Vpi; VGB; IDS; Hysteresis; Vhold; ON state
