akashlevy/NEM-Relay-CAD/figures/quasistatic-curve-labeled.pdf

ON

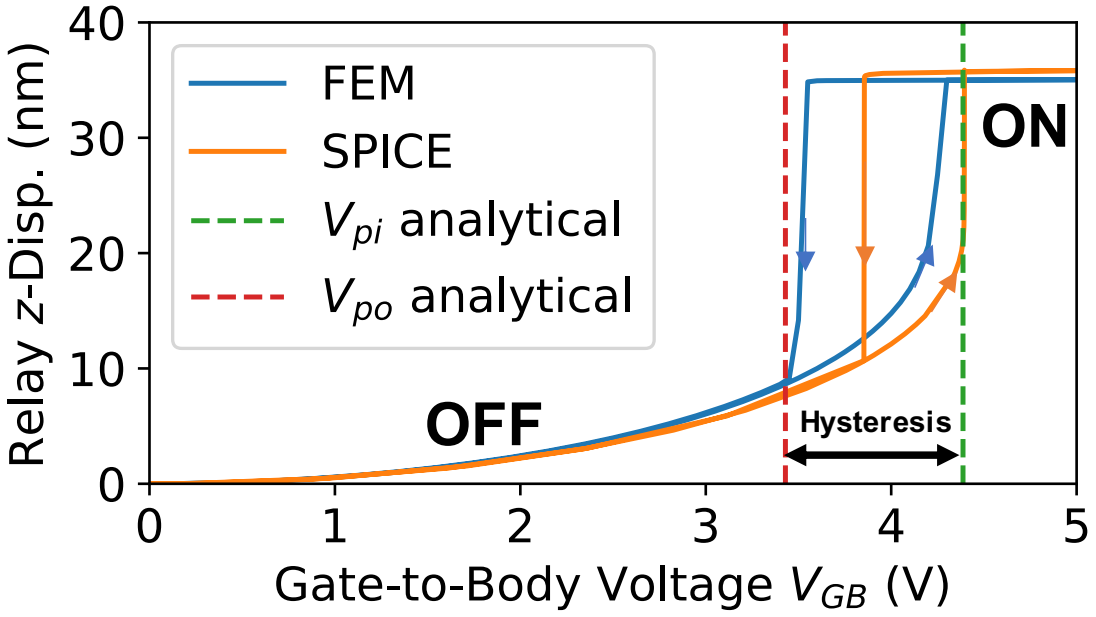
[picture p87: page 1]
OFF; Hysteresis
