akashlevy/NEM-Relay-CAD/figures/icp.pdf

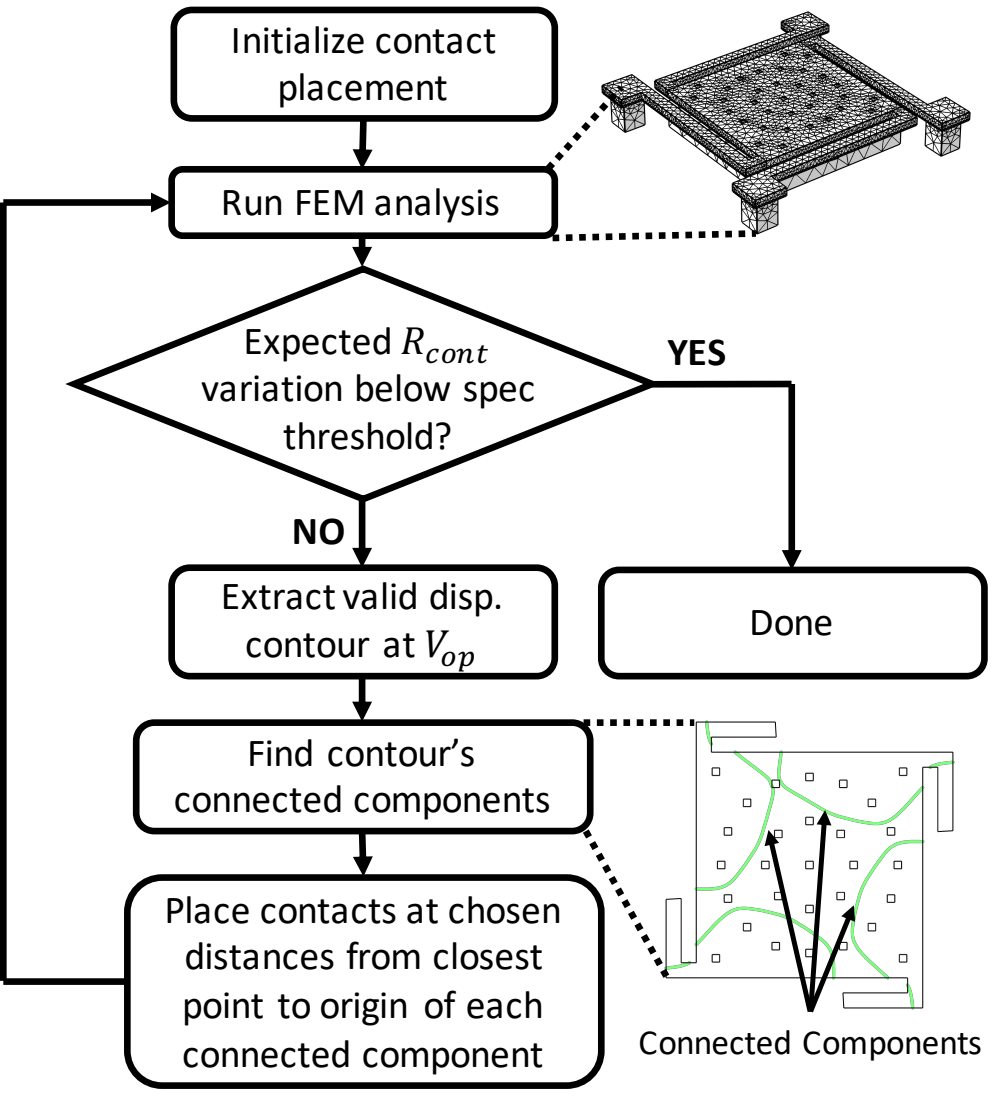
[picture p88: page 1]
Initialize contact placement; Find contour’s connected components; YES; Done; Connected Components

Run FEM analysis

Expected R#!$%
variation below spec
threshold?

Extract valid disp.
contour at V!"

Place contacts at chosen
distances from closest
point to origin of each
connected component
