akashlevy/NEM-Relay-CAD/figures/cgra-comps.pdf

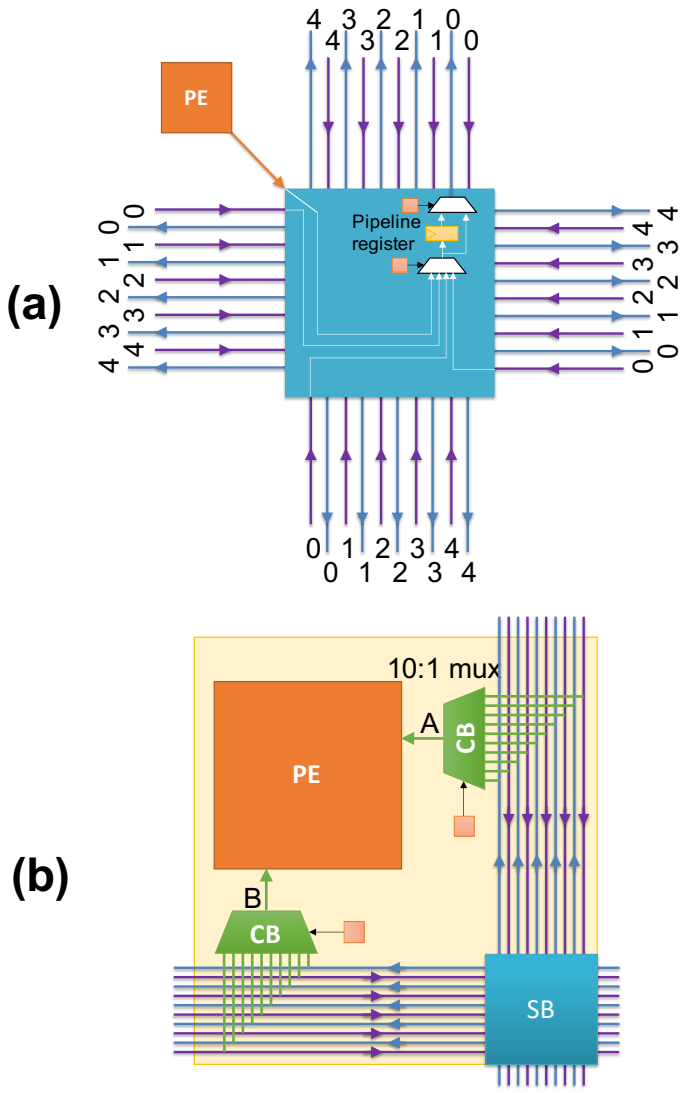
[picture p89: page 1]
Pipeline register; 10:1 mux
