akashlevy/NEM-Relay-CAD/figures/disp-sweep.pdf

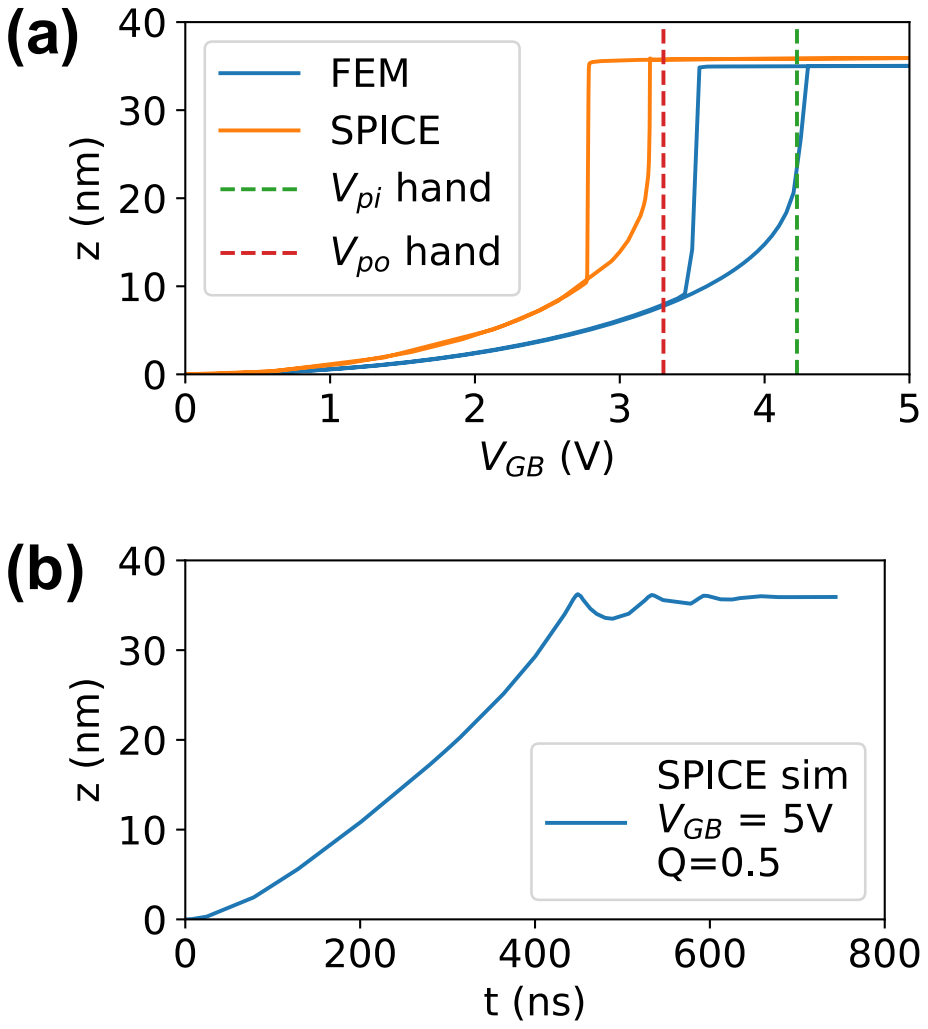
[picture p90: page 1]
