akashlevy/NEM-Relay-CAD/figures/sweeps.pdf

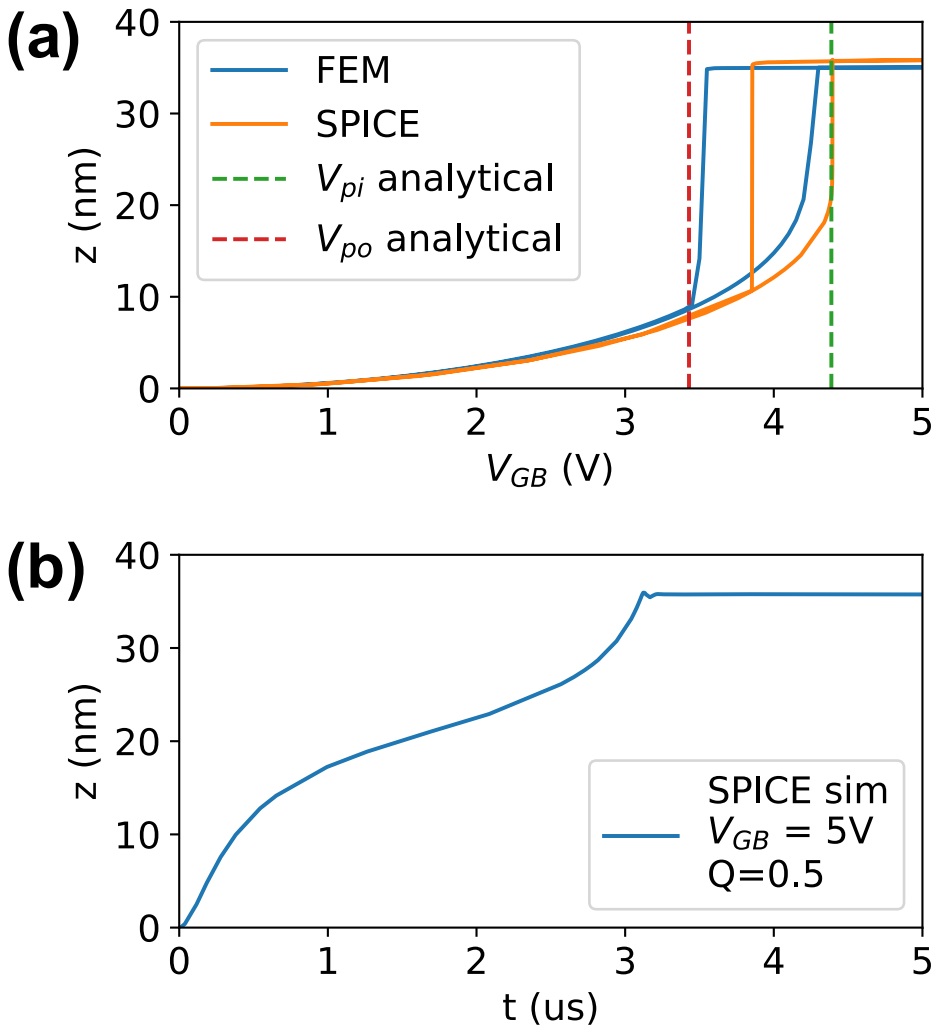
[picture p91: page 1]
