akashlevy/NEM-Relay-CAD/spice/quasistatic_sweep.sp

.title <test_relay.sp>
.hdl nem_relay.va

** Create relay and start at z=0 **
Xnem gnd Vg Vsrc gnd z nem_relay
.ic V(z)=0

** Test fast transitions **
Vsrc Vsrc gnd 1V

** Sweep voltage (unipolar) **
Vg Vg gnd 0V PWL(0s 0V 1000us 0V 2000us 5V 3000us 0V)

** Generate I-V plot **
.tran 0.0001us 3000us

.probe V(Vg) V(Vsrc) PAR('abs(I(Vsrc))') z
.option post=2
.option runlvl=5 accurate

.end
