akashlevy/NEM-Relay-CAD/bench/synth/muxs10.v

/////////////////////////////////////////////////////////////
// Created by: Synopsys DC Ultra(TM) in wire load mode
// Version   : P-2019.03
// Date      : Sat Jun  4 06:43:26 2022
/////////////////////////////////////////////////////////////


module muxs10 ( S, I0, I1, I2, I3, I4, I5, I6, I7, I8, I9, Z );
  input [3:0] S;
  input [7:0] I0;
  input [7:0] I1;
  input [7:0] I2;
  input [7:0] I3;
  input [7:0] I4;
  input [7:0] I5;
  input [7:0] I6;
  input [7:0] I7;
  input [7:0] I8;
  input [7:0] I9;
  output [7:0] Z;
  wire   n65, n66, n67, n68, n69, n70, n71, n72, n73, n74, n75, n76, n77, n78,
         n79, n80, n81, n82, n83, n84, n85, n86, n87, n88, n89, n90, n91, n92,
         n93, n94, n95, n96, n97, n98, n99, n100, n101, n102, n103, n104, n105,
         n106, n107, n108, n109, n110, n111, n112, n113, n114, n115, n116,
         n117, n118, n119, n120;

  INVD1BWP40 U66 ( .I(S[3]), .ZN(n120) );
  INVD1BWP40 U67 ( .I(S[2]), .ZN(n68) );
  ND2D1BWP40 U68 ( .A1(S[1]), .A2(n68), .ZN(n65) );
  NR2D1BWP40 U69 ( .A1(S[0]), .A2(n65), .ZN(n106) );
  INVD1BWP40 U70 ( .I(S[0]), .ZN(n67) );
  NR2D1BWP40 U71 ( .A1(n67), .A2(n65), .ZN(n105) );
  AOI22D1BWP40 U72 ( .A1(n106), .A2(I2[0]), .B1(n105), .B2(I3[0]), .ZN(n73) );
  ND2D1BWP40 U73 ( .A1(S[2]), .A2(S[1]), .ZN(n66) );
  NR2D1BWP40 U74 ( .A1(S[0]), .A2(n66), .ZN(n108) );
  NR2D1BWP40 U75 ( .A1(n67), .A2(n66), .ZN(n107) );
  AOI22D1BWP40 U76 ( .A1(n108), .A2(I6[0]), .B1(n107), .B2(I7[0]), .ZN(n72) );
  NR3D1BWP40 U77 ( .A1(S[0]), .A2(S[1]), .A3(n68), .ZN(n110) );
  IND2D1BWP40 U78 ( .A1(S[1]), .B1(S[0]), .ZN(n69) );
  NR2D1BWP40 U79 ( .A1(n68), .A2(n69), .ZN(n109) );
  AOI22D1BWP40 U80 ( .A1(n110), .A2(I4[0]), .B1(n109), .B2(I5[0]), .ZN(n71) );
  NR3D1BWP40 U81 ( .A1(S[0]), .A2(S[2]), .A3(S[1]), .ZN(n112) );
  NR2D1BWP40 U82 ( .A1(S[2]), .A2(n69), .ZN(n111) );
  AOI22D1BWP40 U83 ( .A1(n112), .A2(I0[0]), .B1(n111), .B2(I1[0]), .ZN(n70) );
  ND4D1BWP40 U84 ( .A1(n73), .A2(n72), .A3(n71), .A4(n70), .ZN(n74) );
  AN2D1BWP40 U85 ( .A1(n112), .A2(S[3]), .Z(n118) );
  AN2D1BWP40 U86 ( .A1(n111), .A2(S[3]), .Z(n117) );
  AO222D1BWP40 U87 ( .A1(n120), .A2(n74), .B1(I8[0]), .B2(n118), .C1(n117), 
        .C2(I9[0]), .Z(Z[0]) );
  AOI22D1BWP40 U88 ( .A1(n106), .A2(I2[6]), .B1(n105), .B2(I3[6]), .ZN(n78) );
  AOI22D1BWP40 U89 ( .A1(n108), .A2(I6[6]), .B1(n107), .B2(I7[6]), .ZN(n77) );
  AOI22D1BWP40 U90 ( .A1(n110), .A2(I4[6]), .B1(n109), .B2(I5[6]), .ZN(n76) );
  AOI22D1BWP40 U91 ( .A1(n112), .A2(I0[6]), .B1(n111), .B2(I1[6]), .ZN(n75) );
  ND4D1BWP40 U92 ( .A1(n78), .A2(n77), .A3(n76), .A4(n75), .ZN(n79) );
  AO222D1BWP40 U93 ( .A1(n120), .A2(n79), .B1(I8[6]), .B2(n118), .C1(n117), 
        .C2(I9[6]), .Z(Z[6]) );
  AOI22D1BWP40 U94 ( .A1(n106), .A2(I2[5]), .B1(n105), .B2(I3[5]), .ZN(n83) );
  AOI22D1BWP40 U95 ( .A1(n108), .A2(I6[5]), .B1(n107), .B2(I7[5]), .ZN(n82) );
  AOI22D1BWP40 U96 ( .A1(n110), .A2(I4[5]), .B1(n109), .B2(I5[5]), .ZN(n81) );
  AOI22D1BWP40 U97 ( .A1(n112), .A2(I0[5]), .B1(n111), .B2(I1[5]), .ZN(n80) );
  ND4D1BWP40 U98 ( .A1(n83), .A2(n82), .A3(n81), .A4(n80), .ZN(n84) );
  AO222D1BWP40 U99 ( .A1(n120), .A2(n84), .B1(I8[5]), .B2(n118), .C1(n117), 
        .C2(I9[5]), .Z(Z[5]) );
  AOI22D1BWP40 U100 ( .A1(n106), .A2(I2[4]), .B1(n105), .B2(I3[4]), .ZN(n88)
         );
  AOI22D1BWP40 U101 ( .A1(n108), .A2(I6[4]), .B1(n107), .B2(I7[4]), .ZN(n87)
         );
  AOI22D1BWP40 U102 ( .A1(n110), .A2(I4[4]), .B1(n109), .B2(I5[4]), .ZN(n86)
         );
  AOI22D1BWP40 U103 ( .A1(n112), .A2(I0[4]), .B1(n111), .B2(I1[4]), .ZN(n85)
         );
  ND4D1BWP40 U104 ( .A1(n88), .A2(n87), .A3(n86), .A4(n85), .ZN(n89) );
  AO222D1BWP40 U105 ( .A1(n120), .A2(n89), .B1(I8[4]), .B2(n118), .C1(n117), 
        .C2(I9[4]), .Z(Z[4]) );
  AOI22D1BWP40 U106 ( .A1(n106), .A2(I2[7]), .B1(n105), .B2(I3[7]), .ZN(n93)
         );
  AOI22D1BWP40 U107 ( .A1(n108), .A2(I6[7]), .B1(n107), .B2(I7[7]), .ZN(n92)
         );
  AOI22D1BWP40 U108 ( .A1(n110), .A2(I4[7]), .B1(n109), .B2(I5[7]), .ZN(n91)
         );
  AOI22D1BWP40 U109 ( .A1(n112), .A2(I0[7]), .B1(n111), .B2(I1[7]), .ZN(n90)
         );
  ND4D1BWP40 U110 ( .A1(n93), .A2(n92), .A3(n91), .A4(n90), .ZN(n94) );
  AO222D1BWP40 U111 ( .A1(n120), .A2(n94), .B1(I8[7]), .B2(n118), .C1(I9[7]), 
        .C2(n117), .Z(Z[7]) );
  AOI22D1BWP40 U112 ( .A1(n106), .A2(I2[3]), .B1(n105), .B2(I3[3]), .ZN(n98)
         );
  AOI22D1BWP40 U113 ( .A1(n108), .A2(I6[3]), .B1(n107), .B2(I7[3]), .ZN(n97)
         );
  AOI22D1BWP40 U114 ( .A1(n110), .A2(I4[3]), .B1(n109), .B2(I5[3]), .ZN(n96)
         );
  AOI22D1BWP40 U115 ( .A1(n112), .A2(I0[3]), .B1(n111), .B2(I1[3]), .ZN(n95)
         );
  ND4D1BWP40 U116 ( .A1(n98), .A2(n97), .A3(n96), .A4(n95), .ZN(n99) );
  AO222D1BWP40 U117 ( .A1(n120), .A2(n99), .B1(I8[3]), .B2(n118), .C1(n117), 
        .C2(I9[3]), .Z(Z[3]) );
  AOI22D1BWP40 U118 ( .A1(n106), .A2(I2[2]), .B1(n105), .B2(I3[2]), .ZN(n103)
         );
  AOI22D1BWP40 U119 ( .A1(n108), .A2(I6[2]), .B1(n107), .B2(I7[2]), .ZN(n102)
         );
  AOI22D1BWP40 U120 ( .A1(n110), .A2(I4[2]), .B1(n109), .B2(I5[2]), .ZN(n101)
         );
  AOI22D1BWP40 U121 ( .A1(n112), .A2(I0[2]), .B1(n111), .B2(I1[2]), .ZN(n100)
         );
  ND4D1BWP40 U122 ( .A1(n103), .A2(n102), .A3(n101), .A4(n100), .ZN(n104) );
  AO222D1BWP40 U123 ( .A1(n120), .A2(n104), .B1(I8[2]), .B2(n118), .C1(n117), 
        .C2(I9[2]), .Z(Z[2]) );
  AOI22D1BWP40 U124 ( .A1(n106), .A2(I2[1]), .B1(n105), .B2(I3[1]), .ZN(n116)
         );
  AOI22D1BWP40 U125 ( .A1(n108), .A2(I6[1]), .B1(n107), .B2(I7[1]), .ZN(n115)
         );
  AOI22D1BWP40 U126 ( .A1(n110), .A2(I4[1]), .B1(n109), .B2(I5[1]), .ZN(n114)
         );
  AOI22D1BWP40 U127 ( .A1(n112), .A2(I0[1]), .B1(n111), .B2(I1[1]), .ZN(n113)
         );
  ND4D1BWP40 U128 ( .A1(n116), .A2(n115), .A3(n114), .A4(n113), .ZN(n119) );
  AO222D1BWP40 U129 ( .A1(n120), .A2(n119), .B1(I8[1]), .B2(n118), .C1(n117), 
        .C2(I9[1]), .Z(Z[1]) );
endmodule
